antmicro/gpu-cluster-backplane/assets/previews/layer0.png

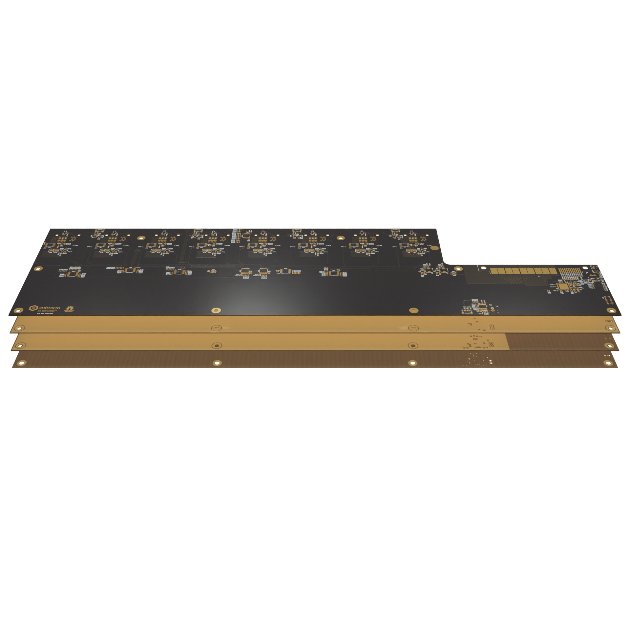
assets/previews/layer0.png
