antmicro/gpu-cluster-backplane/assets/previews/layer2.png

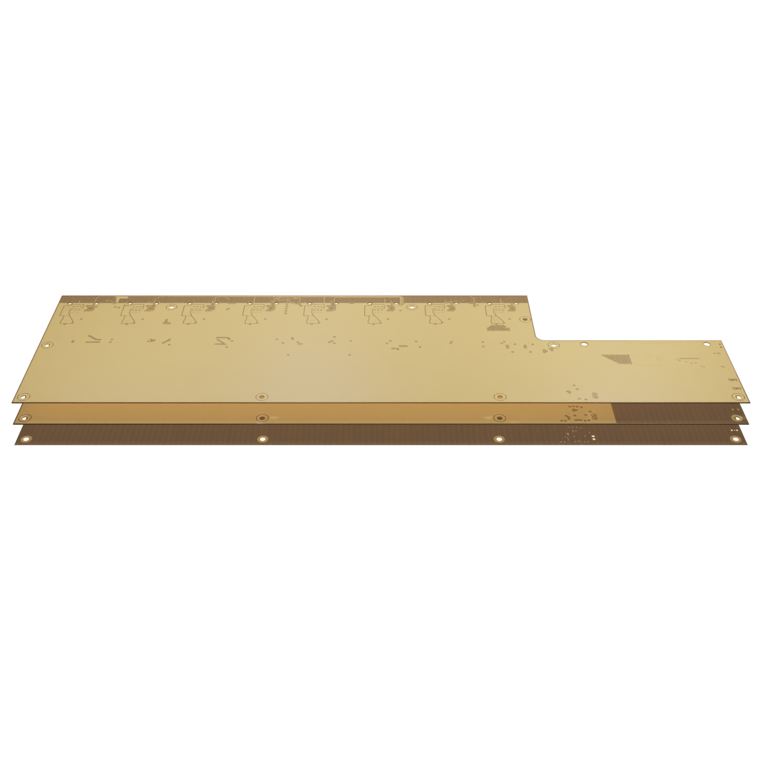
assets/previews/layer2.png
