antmicro/gpu-cluster-backplane/assets/previews/leftB.png

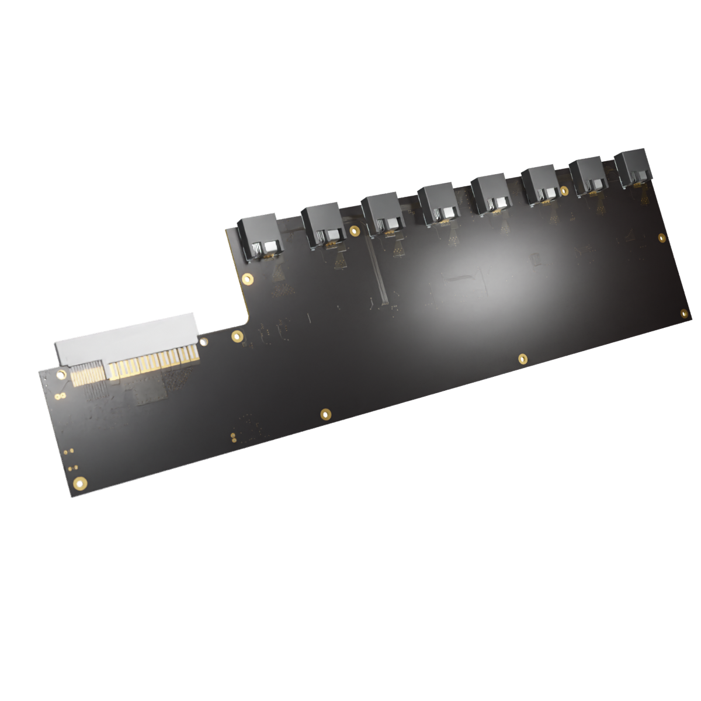
assets/previews/leftB.png
