antmicro/gpu-cluster-backplane/assets/previews/leftT.png

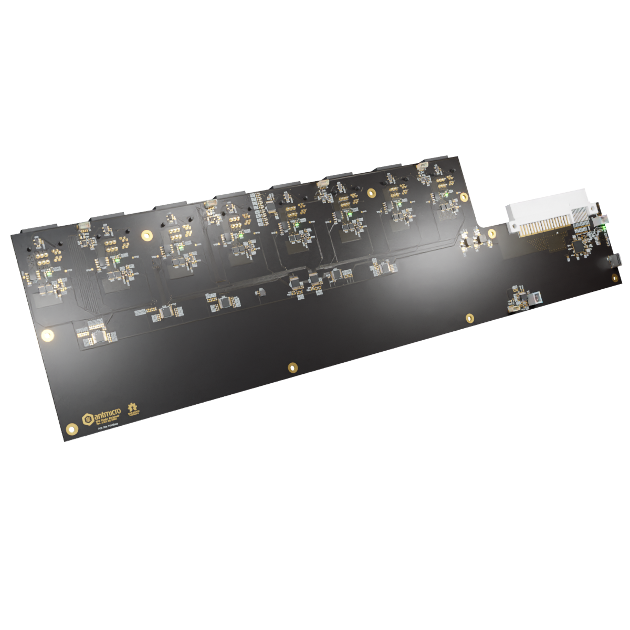
assets/previews/leftT.png
