antmicro/gpu-cluster-backplane/assets/previews/orthoB.png

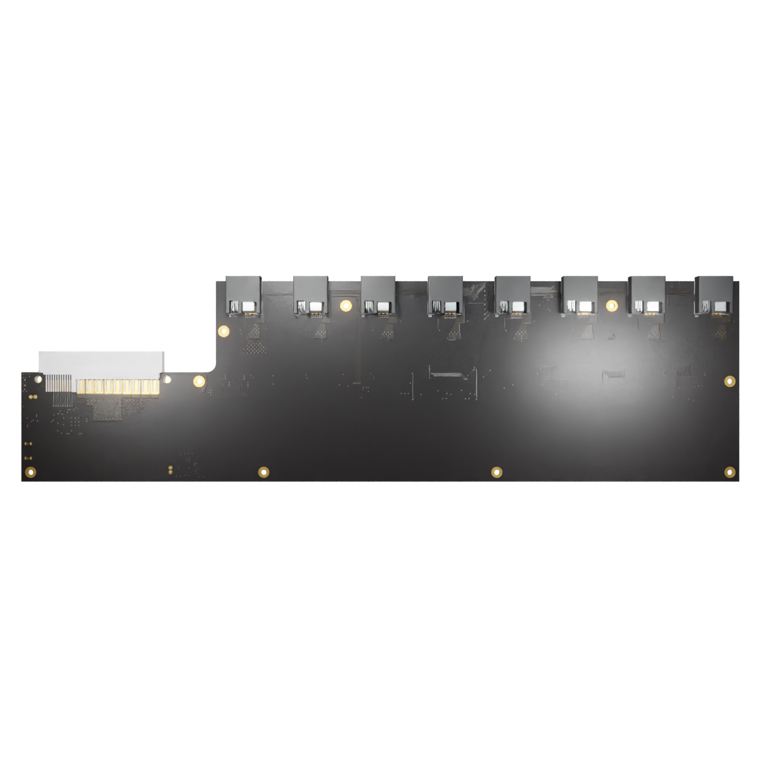
assets/previews/orthoB.png
