antmicro/gpu-cluster-backplane/assets/previews/orthoB_thumbnail.png

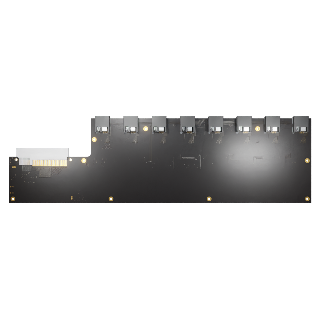
assets/previews/orthoB_thumbnail.png
