antmicro/gpu-cluster-backplane/assets/previews/orthoT.png

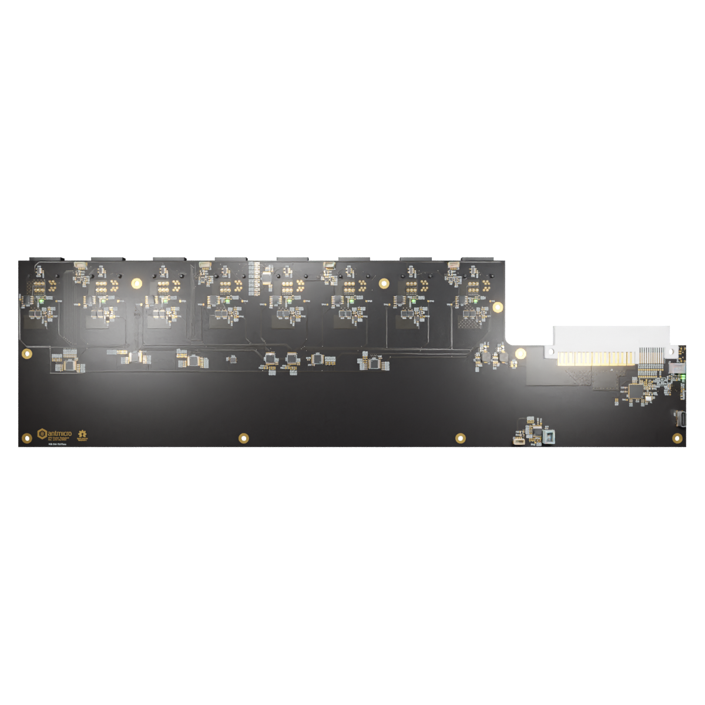
assets/previews/orthoT.png
