antmicro/gpu-cluster-backplane/assets/previews/photoB.png

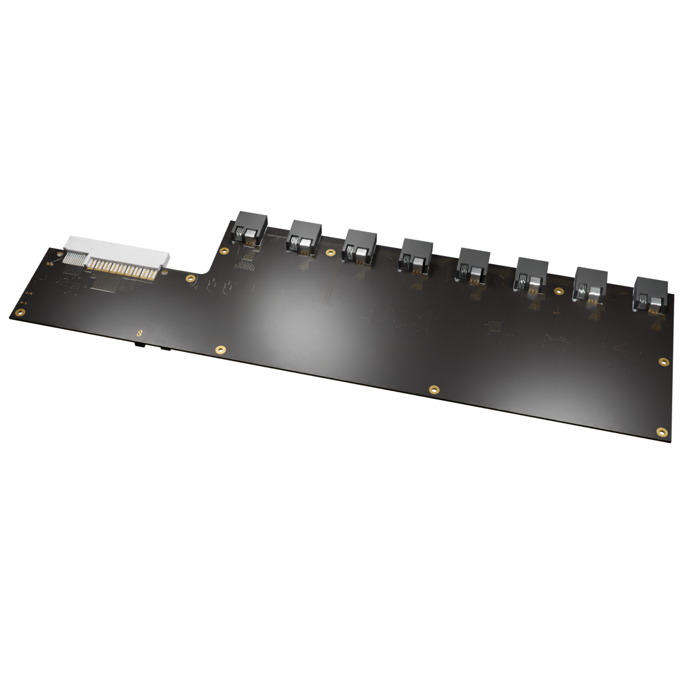
assets/previews/photoB.png
