antmicro/gpu-cluster-backplane/assets/previews/photoT.png

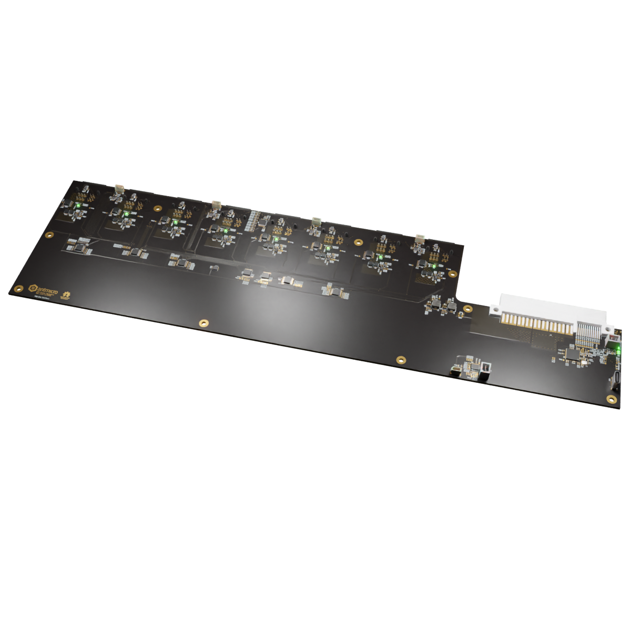
assets/previews/photoT.png
