antmicro/gpu-cluster-backplane/assets/previews/rightB.png

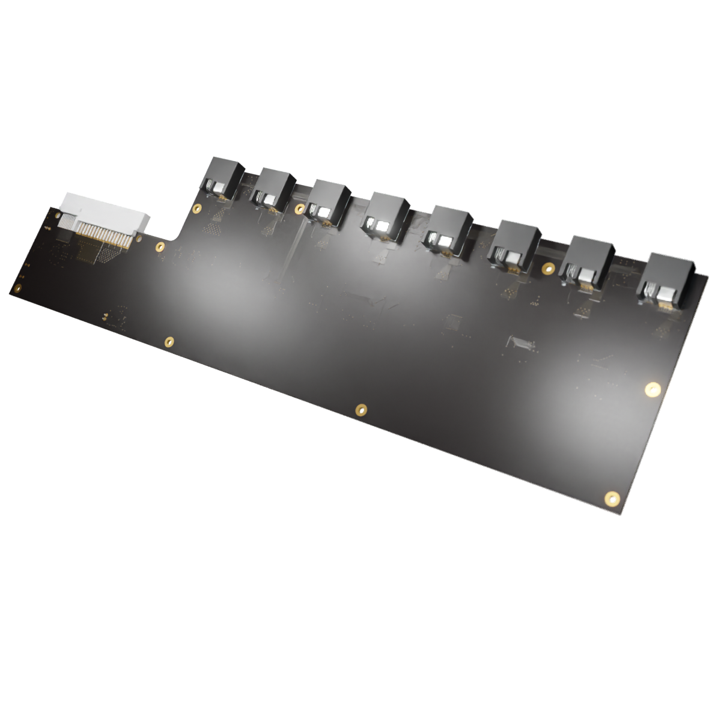
assets/previews/rightB.png
