antmicro/gpu-cluster-backplane/assets/previews/rightT.png

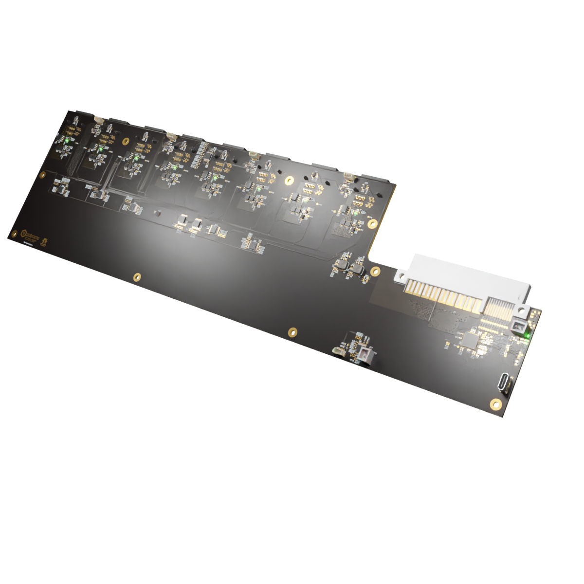
assets/previews/rightT.png
