antmicro/gpu-cluster-backplane/GPU-output.kicad_sch

## KiCad design GPU-output.kicad_sch (2023-11-16)

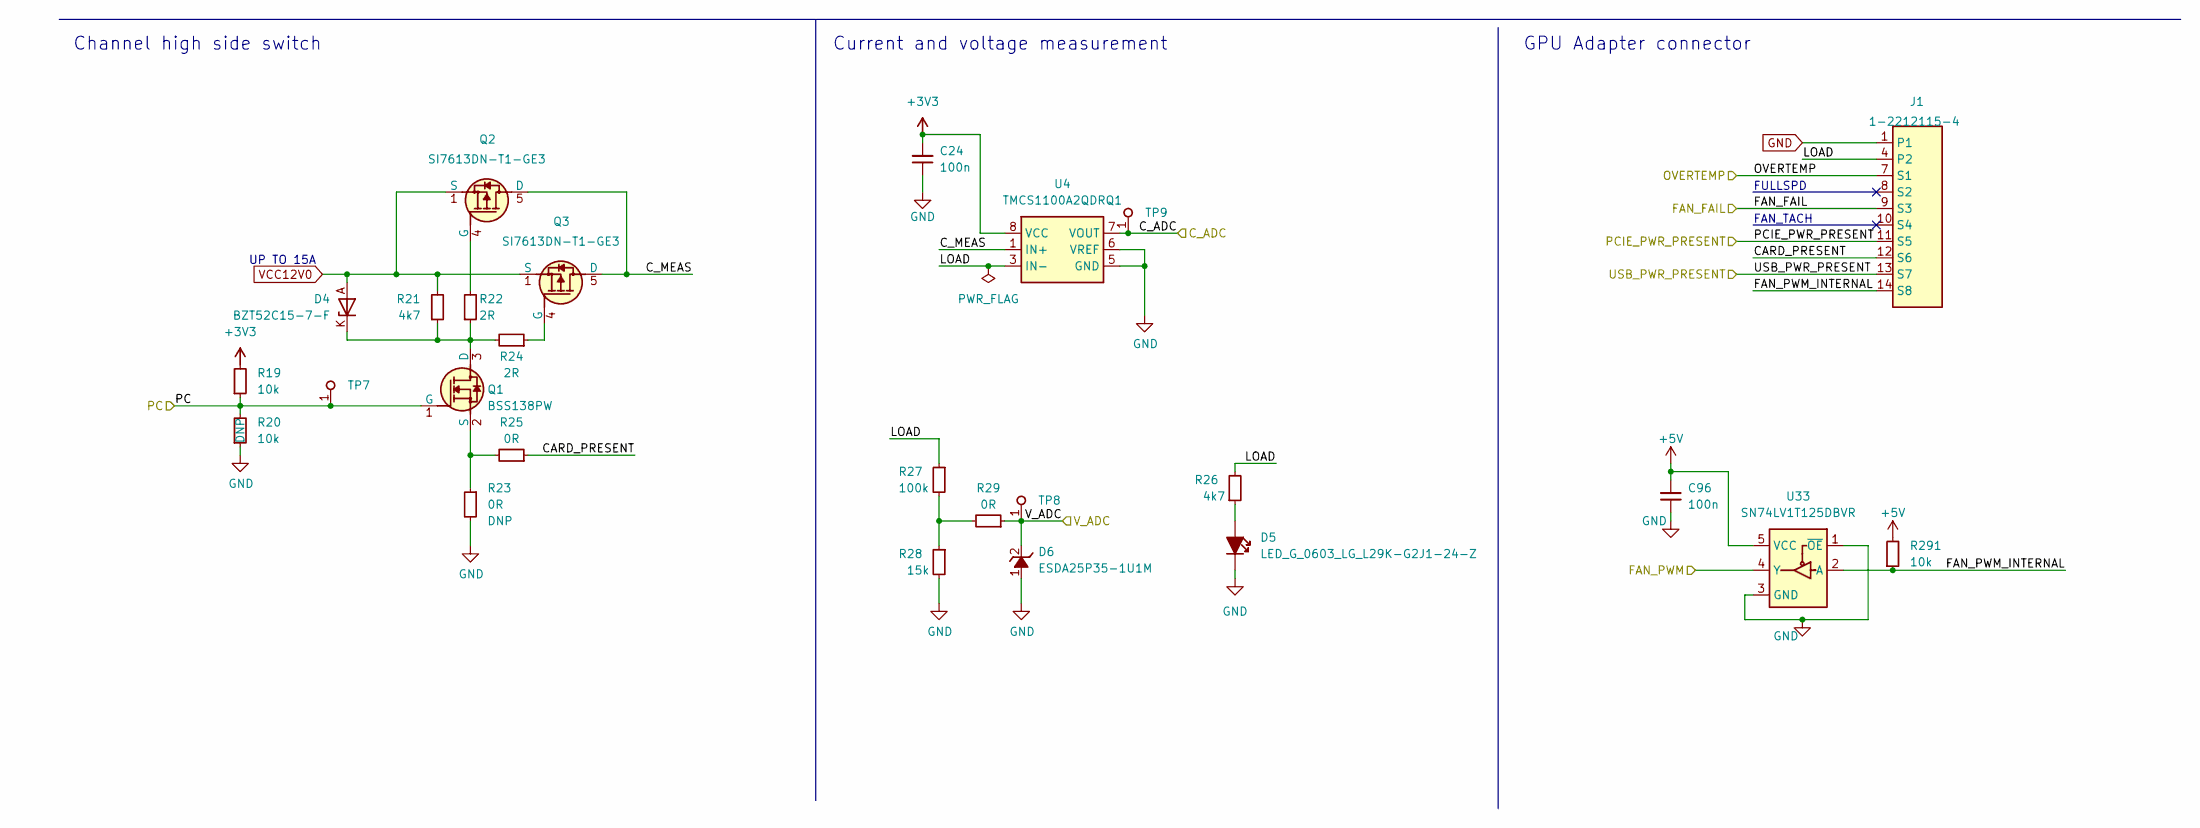
[picture p28: schematic GPU-output.kicad_sch]

Parts:
C24, C96: C_100n_0402; C_0402_1005Metric; Voltage 50V; MPN GRM155R61H104KE14D
D4: BZT52C15-7-F; D_SOD-123F; MPN BZT52C15-7-F
D5: LED_G_0603_LG_L29K-G2J1-24-Z; LED_0603_1608Metric_G; MPN LG L29K-G2J1-24-Z
D6: ESDA25P35-1U1M; MPN ESDA25P35-1U1M
J1: Conn_1-2212115-4; MPN 1-2212115-4
Q1: BSS138PW; SC70-3; MPN BSS138PW
Q2, Q3: SI7613DN-T1-GE3; Vishay_PowerPAK_1212-8_Single; MPN SI7613DN-T1-GE3
R19, R20, R291: R_10k_0402; R_0402_1005Metric; Tolerance 1%; MPN CR0402-FX-1002GLF
R21, R26: R_4k7_0402; R_0402_1005Metric; Tolerance 1%; MPN CR0402-FX-4701GLF
R22, R24: R_2R_0402; R_0402_1005Metric; Tolerance 1%; MPN CR0402-FX-2R00GLF
R23, R25, R29: R_0R_0402; R_0402_1005Metric; MPN ERJ2GE0R00X
R27: R_100k_0402; R_0402_1005Metric; Tolerance 1%; MPN CR0402-FX-1003GLF
R28: R_15k_0.1%_0402; R_0402_1005Metric; Tolerance 0.1%; MPN ERA-2ARB153X
TP7, TP8, TP9: TP_1mm_SMD; TP_SMD_1mm
U4: TMCS1100A2-Q1; SOIC-8_3.9x4.9x1.75mm_P1.27mm; MPN TMCS1100A2QDRQ1
U33: SN74LV1T125DBVR; SOT-23-5; MPN SN74LV1T125DBVR

Connections:
+3V3: C24.2, R19.2, U4.8 (VCC)
+5V: C96.2, R291.2, U33.5 (VCC)
CARD_PRESENT: J1.12 (S6), R25.1
C_ADC: TP9.1, U4.7 (VOUT)
C_MEAS: Q2.5 (D), Q3.5 (D), U4.1 (IN+), U4.2 (IN+)
FAN_FAIL: J1.9 (S3)
FAN_PWM: U33.4 (Y)
FAN_PWM_INTERNAL: J1.14 (S8), R291.1, U33.2 (A)
GND: C24.1, C96.1, D5.2, D6.1 (K), J1.1, R20.1, R23.2, R28.2, U4.5 (GND), U4.6 (VREF), U33.1 (~OE), U33.3 (GND)
LOAD: J1.4 (P2), R26.2, R27.1, U4.3 (IN-), U4.4 (IN-)
unnamed: D4.K, Q1.3 (D), R21.1, R22.1, R24.2
unnamed: D5.1, R26.1
unnamed: Q1.2 (S), R23.1, R25.2
unnamed: Q2.4 (G), R22.2
unnamed: Q3.4 (G), R24.1
unnamed: R27.2, R28.1, R29.2
OVERTEMP: J1.7 (S1)
PC: Q1.1 (G), R19.1, R20.2, TP7.1
PCIE_PWR_PRESENT: J1.11 (S5)
USB_PWR_PRESENT: J1.13 (S7)
VCC12V0: D4.A, Q2.1 (S), Q2.2 (S), Q2.3 (S), Q3.1 (S), Q3.2 (S), Q3.3 (S), R21.2
V_ADC: D6.2 (A), R29.1, TP8.1

Notes on the sheet:
UP TO 15A
FAN_TACH
Channel high side switch
GPU Adapter connector
Current and voltage measurement
FULLSPD
