antmicro/gpu-cluster-backplane/connectors.kicad_sch

## KiCad design connectors.kicad_sch (2023-11-16)

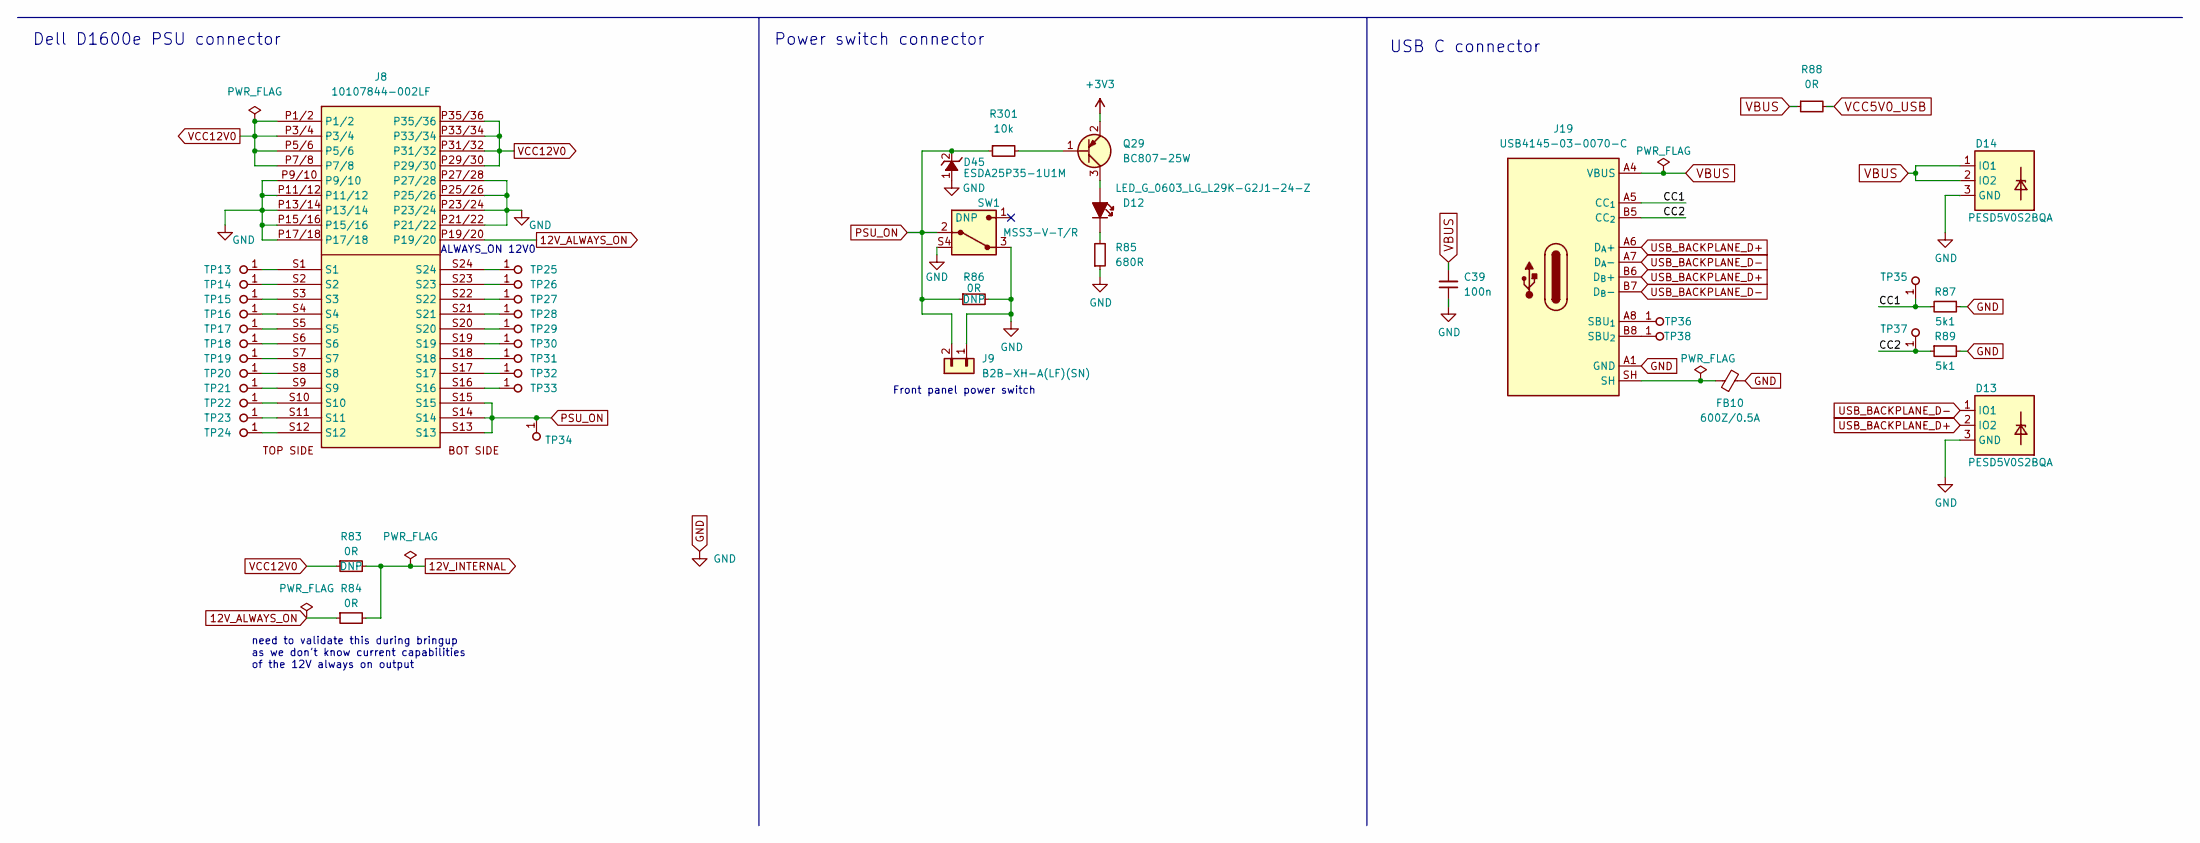
[picture p29: schematic connectors.kicad_sch]

Parts:
C39: C_100n_0402; C_0402_1005Metric; Voltage 50V; MPN GRM155R61H104KE14D
D12: LED_G_0603_LG_L29K-G2J1-24-Z; LED_0603_1608Metric_G; MPN LG L29K-G2J1-24-Z
D13, D14: PESD5V0S2BQA; TPD2E009DRTR; MPN PESD5V0S2BQA
D45: ESDA25P35-1U1M; MPN ESDA25P35-1U1M
FB10: FB_600Z_0.5A_Murata-BLM18AG_0603; FB_0603_1608Metric; MPN BLM18AG601SN1D
J8: Socket_10107844-002LF; MPN 10107844-002LF
J9: JST_XH_1x2_B2B-XH-A-LF-SN; Conn_JST_XH_1x2_B2B-XH-A-LF-SN; MPN B2B-XH-A(LF)(SN)
J19: USB-C_GCT_USB4145-03-0070-C; USB-C_Receptacle_GCT_USB4145-03-0070-C; MPN USB4145-03-0070-C
Q29: BC807-25W; SOT-323; MPN SBC807-40WT1G
R83, R84: R_0R_0805; R_0805_2012Metric; MPN CRCW08050000Z0EA
R85: R_680R_0402; R_0402_1005Metric; Tolerance 1%; MPN CR0402-FX-6800GLF
R86, R88: R_0R_0402; R_0402_1005Metric; MPN ERJ2GE0R00X
R87, R89: R_5k1_0402; R_0402_1005Metric; Tolerance 1%; MPN CR0402-FX-5101GLF
R301: R_10k_0402; R_0402_1005Metric; Tolerance 1%; MPN CR0402-FX-1002GLF
SW1: MSS3-V-T_R; Switch_Slide_MSS3; MPN MSS3-V-T/R
TP13, TP14, TP15, TP16, TP17, TP18, TP19, TP20, TP21, TP22, TP23, TP24, TP25, TP26, TP27, TP28, TP29, TP30, TP31, TP32, TP33, TP34, TP35, TP36, TP37, TP38: TP_1mm_SMD; TP_SMD_1mm

Connections:
12V_ALWAYS_ON: J8.P19/20, R84.1
12V_INTERNAL: R83.2, R84.2
+3V3: Q29.2
CC1: J19.A5 (CC_{1}), R87.2, TP35.1
CC2: J19.B5 (CC_{2}), R89.1, TP37.1
GND: C39.1, D13.3 (GND), D14.3 (GND), D45.1 (K), FB10.2, J8.P9/10, J8.P11/12, J8.P13/14, J8.P15/16, J8.P17/18, J8.P21/22, J8.P23/24, J8.P25/26, J8.P27/28, J9.1, J19.A1 (GND), J19.A12 (GND), J19.B1 (GND), J19.B12 (GND), R85.1, R86.2, R87.1, R89.2, SW1.3, SW1.S1 (SH), SW1.S2 (SH), SW1.S3 (SH), SW1.S4 (SH)
unnamed: D12.1, Q29.3
unnamed: D12.2, R85.2
unnamed: FB10.1, J19.SH
unnamed: J8.S1, TP13.1
unnamed: J8.S2, TP14.1
unnamed: J8.S3, TP15.1
unnamed: J8.S4, TP16.1
unnamed: J8.S5, TP17.1
unnamed: J8.S6, TP18.1
unnamed: J8.S7, TP19.1
unnamed: J8.S8, TP20.1
unnamed: J8.S9, TP21.1
unnamed: J8.S10, TP22.1
unnamed: J8.S11, TP23.1
unnamed: J8.S12, TP24.1
unnamed: J8.S16, TP33.1
unnamed: J8.S17, TP32.1
unnamed: J8.S18, TP31.1
unnamed: J8.S19, TP30.1
unnamed: J8.S20, TP29.1
unnamed: J8.S21, TP28.1
unnamed: J8.S22, TP27.1
unnamed: J8.S23, TP26.1
unnamed: J8.S24, TP25.1
unnamed: J19.A8 (SBU_{1}), TP36.1
unnamed: J19.B8 (SBU_{2}), TP38.1
unnamed: Q29.1, R301.2
PSU_ON: D45.2 (A), J8.S13, J8.S14, J8.S15, J9.2, R86.1, R301.1, SW1.2, TP34.1
USB_BACKPLANE_D+: D13.2 (IO2), J19.A6 (D_{A}+), J19.B6 (D_{B}+)
USB_BACKPLANE_D-: D13.1 (IO1), J19.A7 (D_{A}-), J19.B7 (D_{B}-)
VBUS: C39.2, D14.1 (IO1), D14.2 (IO2), J19.A4 (VBUS), J19.A9 (VBUS), J19.B4 (VBUS), J19.B9 (VBUS), R88.1
VCC5V0_USB: R88.2
VCC12V0: J8.P1/2, J8.P3/4, J8.P5/6, J8.P7/8, J8.P29/30, J8.P31/32, J8.P33/34, J8.P35/36, R83.1

Notes on the sheet:
Dell D1600e PSU connector
Power switch connector
need to validate this during bringup as we don't know current capabilities of the 12V always on output
USB C connector
Front panel power switch
ALWAYS_ON 12V0
