antmicro/gpu-cluster-backplane/debug-signals.kicad_sch

## KiCad design debug-signals.kicad_sch (2023-11-15)

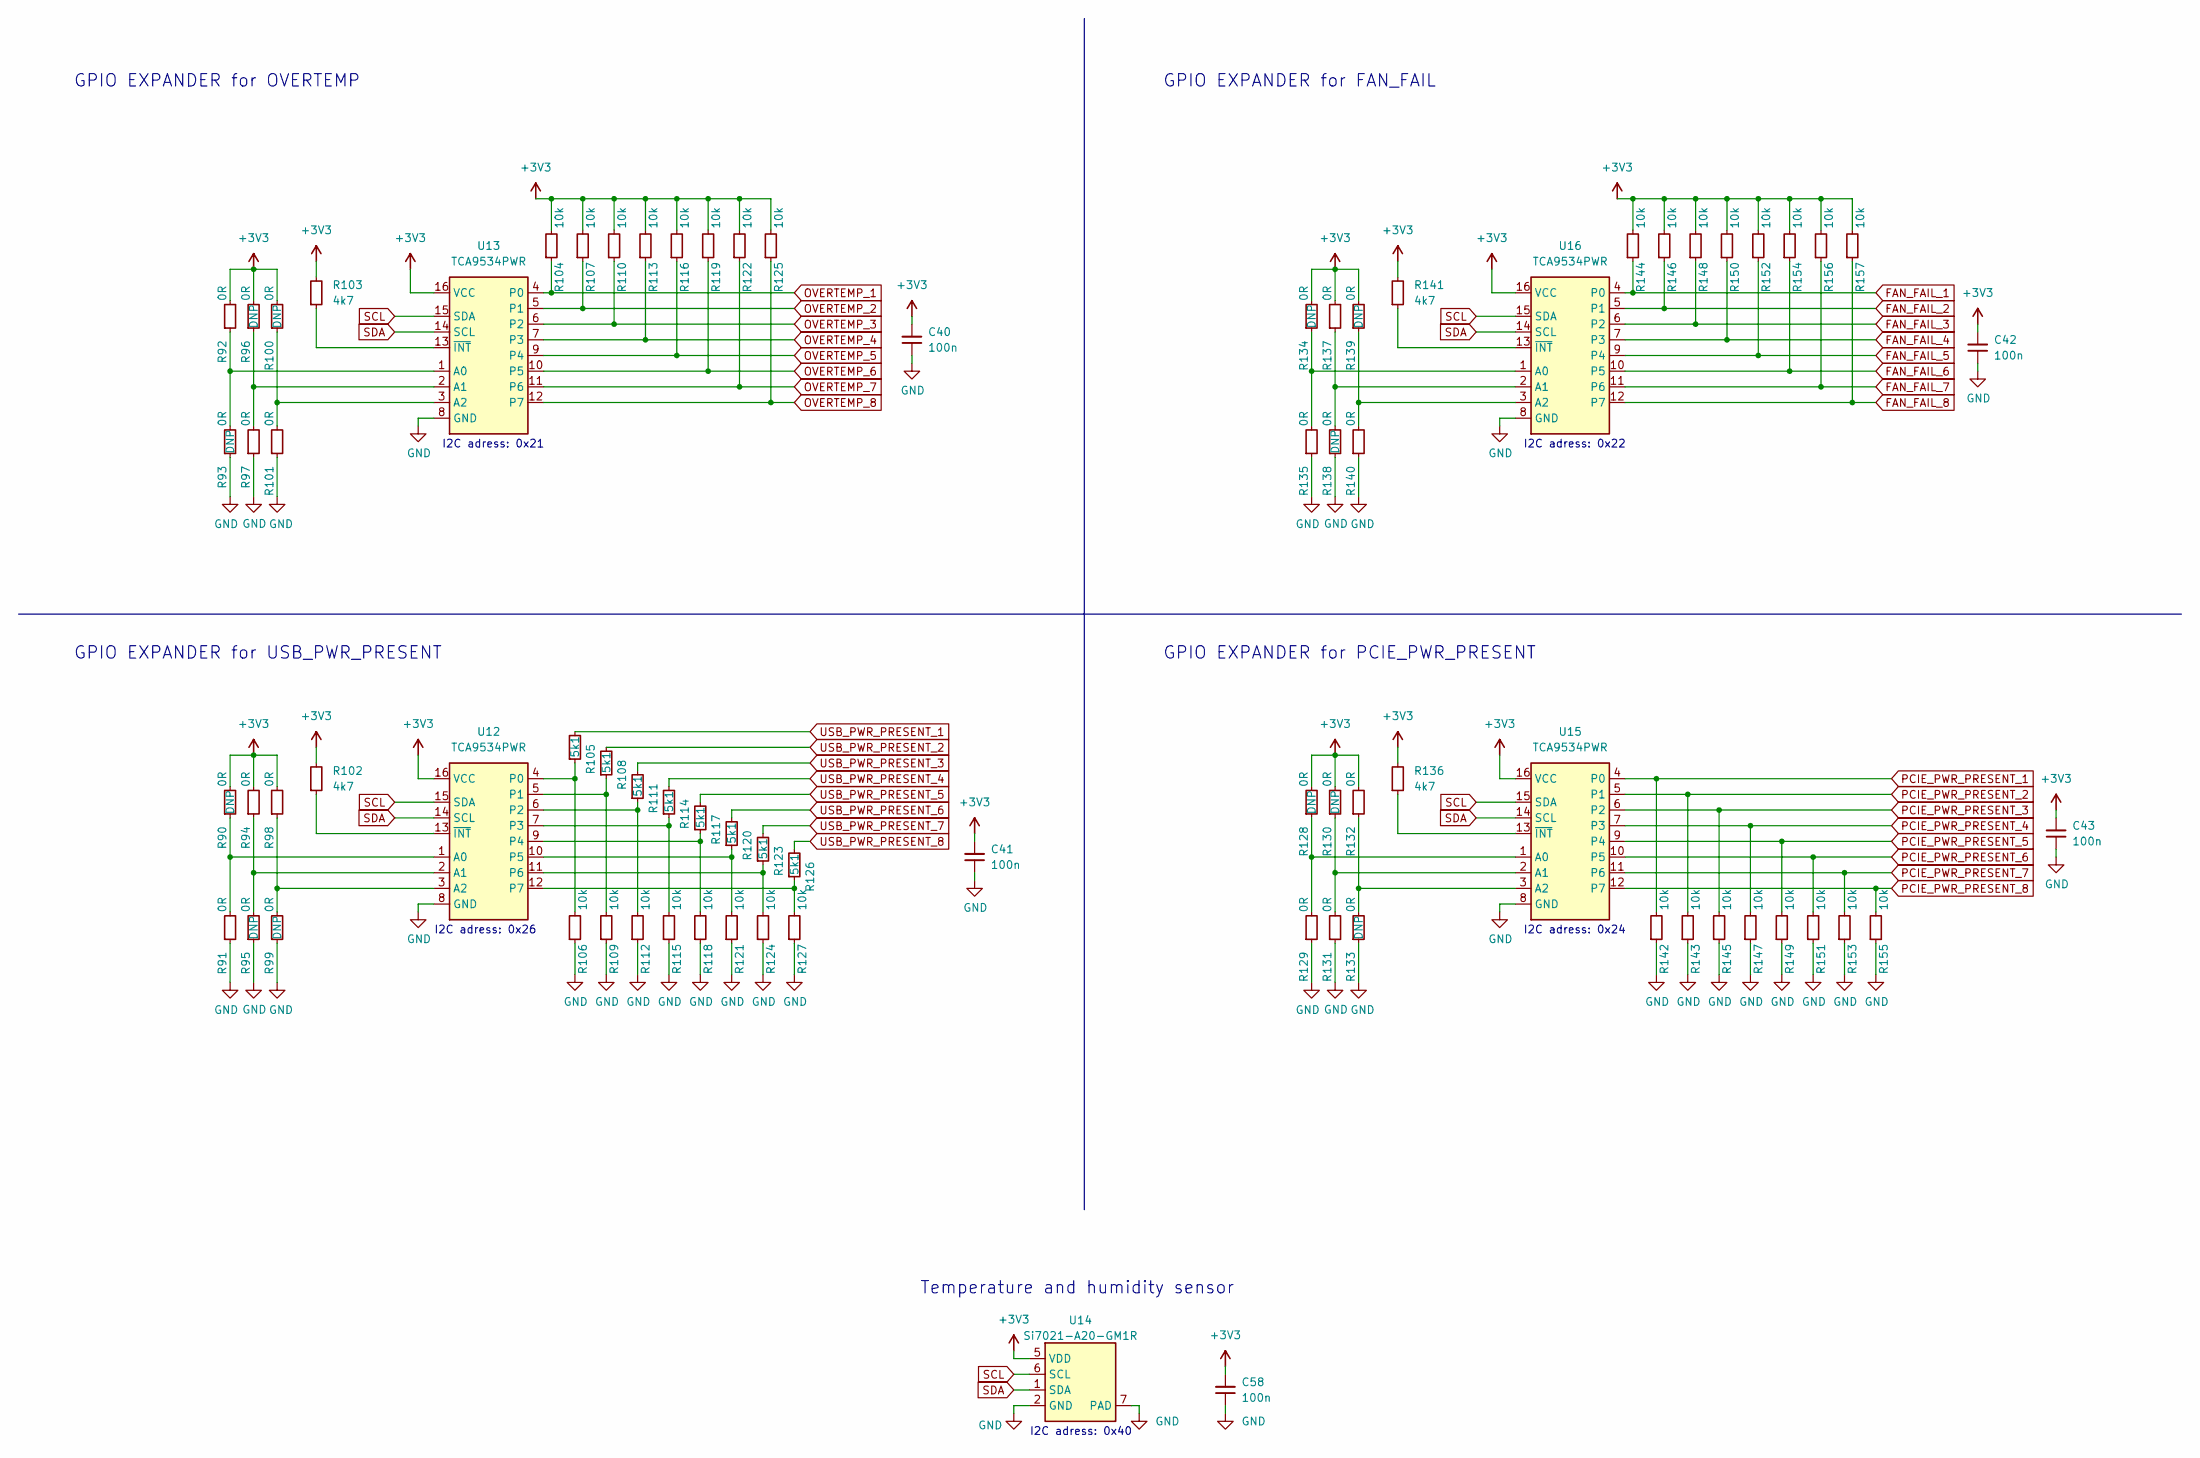
[picture p30: schematic debug-signals.kicad_sch]

Parts:
C40, C41, C42, C43, C58: C_100n_0402; C_0402_1005Metric; Voltage 50V; MPN GRM155R61H104KE14D
R90, R91, R92, R93, R94, R95, R96, R97, R98, R99, R100, R101, R128, R129, R130, R131, R132, R133, R134, R135, R137, R138, R139, R140: R_0R_0402; R_0402_1005Metric; MPN ERJ2GE0R00X
R102, R103, R136, R141: R_4k7_0402; R_0402_1005Metric; Tolerance 1%; MPN CR0402-FX-4701GLF
R104, R106, R107, R109, R110, R112, R113, R115, R116, R118, R119, R121, R122, R124, R125, R127, R142, R143, R144, R145, R146, R147, R148, R149, R150, R151, R152, R153, R154, R155, R156, R157: R_10k_0402; R_0402_1005Metric; Tolerance 1%; MPN CR0402-FX-1002GLF
R105, R108, R111, R114, R117, R120, R123, R126: R_5k1_0402; R_0402_1005Metric; Tolerance 1%; MPN CR0402-FX-5101GLF
U12, U13, U15, U16: TCA9534PWR_TSSOP; TSSOP-16_4.4x5mm_P0.65mm; MPN TCA9534PWR
U14: Si7021; DFN-6-1EP_3x3mm_P1mm_EP1.5x2.4mm; MPN Si7021-A20-GM1R

Connections:
+3V3: C40.2, C41.2, C42.2, C43.2, C58.2, R90.2, R92.2, R94.2, R96.2, R98.2, R100.2, R102.2, R103.2, R104.2, R107.2, R110.2, R113.2, R116.2, R119.2, R122.2, R125.2, R128.2, R130.2, R132.2, R134.2, R136.2, R137.2, R139.2, R141.2, R144.2, R146.2, R148.2, R150.2, R152.2, R154.2, R156.2, R157.2, U12.16 (VCC), U13.16 (VCC), U14.5 (VDD), U15.16 (VCC), U16.16 (VCC)
FAN_FAIL_1: R144.1, U16.4 (P0)
FAN_FAIL_2: R146.1, U16.5 (P1)
FAN_FAIL_3: R148.1, U16.6 (P2)
FAN_FAIL_4: R150.1, U16.7 (P3)
FAN_FAIL_5: R152.1, U16.9 (P4)
FAN_FAIL_6: R154.1, U16.10 (P5)
FAN_FAIL_7: R156.1, U16.11 (P6)
FAN_FAIL_8: R157.1, U16.12 (P7)
GND: C40.1, C41.1, C42.1, C43.1, C58.1, R91.1, R93.1, R95.1, R97.1, R99.1, R101.1, R106.1, R109.1, R112.1, R115.1, R118.1, R121.1, R124.1, R127.1, R129.1, R131.1, R133.1, R135.1, R138.1, R140.1, R142.1, R143.1, R145.1, R147.1, R149.1, R151.1, R153.1, R155.1, U12.8 (GND), U13.8 (GND), U14.2 (GND), U14.7 (PAD), U15.8 (GND), U16.8 (GND)
unnamed: R90.1, R91.2, U12.1 (A0)
unnamed: R92.1, R93.2, U13.1 (A0)
unnamed: R94.1, R95.2, U12.2 (A1)
unnamed: R96.1, R97.2, U13.2 (A1)
unnamed: R98.1, R99.2, U12.3 (A2)
unnamed: R100.1, R101.2, U13.3 (A2)
unnamed: R102.1, U12.13 (~INT)
unnamed: R103.1, U13.13 (~INT)
unnamed: R105.1, R106.2, U12.4 (P0)
unnamed: R108.1, R109.2, U12.5 (P1)
unnamed: R111.1, R112.2, U12.6 (P2)
unnamed: R114.1, R115.2, U12.7 (P3)
unnamed: R117.1, R118.2, U12.9 (P4)
unnamed: R120.1, R121.2, U12.10 (P5)
unnamed: R123.1, R124.2, U12.11 (P6)
unnamed: R126.1, R127.2, U12.12 (P7)
unnamed: R128.1, R129.2, U15.1 (A0)
unnamed: R130.1, R131.2, U15.2 (A1)
unnamed: R132.1, R133.2, U15.3 (A2)
unnamed: R134.1, R135.2, U16.1 (A0)
unnamed: R136.1, U15.13 (~INT)
unnamed: R137.1, R138.2, U16.2 (A1)
unnamed: R139.1, R140.2, U16.3 (A2)
unnamed: R141.1, U16.13 (~INT)
OVERTEMP_1: R104.1, U13.4 (P0)
OVERTEMP_2: R107.1, U13.5 (P1)
OVERTEMP_3: R110.1, U13.6 (P2)
OVERTEMP_4: R113.1, U13.7 (P3)
OVERTEMP_5: R116.1, U13.9 (P4)
OVERTEMP_6: R119.1, U13.10 (P5)
OVERTEMP_7: R122.1, U13.11 (P6)
OVERTEMP_8: R125.1, U13.12 (P7)
PCIE_PWR_PRESENT_1: R142.2, U15.4 (P0)
PCIE_PWR_PRESENT_2: R143.2, U15.5 (P1)
PCIE_PWR_PRESENT_3: R145.2, U15.6 (P2)
PCIE_PWR_PRESENT_4: R147.2, U15.7 (P3)
PCIE_PWR_PRESENT_5: R149.2, U15.9 (P4)
PCIE_PWR_PRESENT_6: R151.2, U15.10 (P5)
PCIE_PWR_PRESENT_7: R153.2, U15.11 (P6)
PCIE_PWR_PRESENT_8: R155.2, U15.12 (P7)
SCL: U12.15 (SDA), U13.15 (SDA), U14.6 (SCL), U15.15 (SDA), U16.15 (SDA)
SDA: U12.14 (SCL), U13.14 (SCL), U14.1 (SDA), U15.14 (SCL), U16.14 (SCL)
USB_PWR_PRESENT_1: R105.2
USB_PWR_PRESENT_2: R108.2
USB_PWR_PRESENT_3: R111.2
USB_PWR_PRESENT_4: R114.2
USB_PWR_PRESENT_5: R117.2
USB_PWR_PRESENT_6: R120.2
USB_PWR_PRESENT_7: R123.2
USB_PWR_PRESENT_8: R126.2

Notes on the sheet:
GPIO EXPANDER for PCIE_PWR_PRESENT
GPIO EXPANDER for FAN_FAIL
I2C adress: 0x21
I2C adress: 0x26
I2C adress: 0x22
I2C adress: 0x24
Temperature and humidity sensor
GPIO EXPANDER for USB_PWR_PRESENT
I2C adress: 0x40
GPIO EXPANDER for OVERTEMP
