antmicro/gpu-cluster-backplane/fans-control.kicad_sch

## KiCad design fans-control.kicad_sch (2023-11-16)

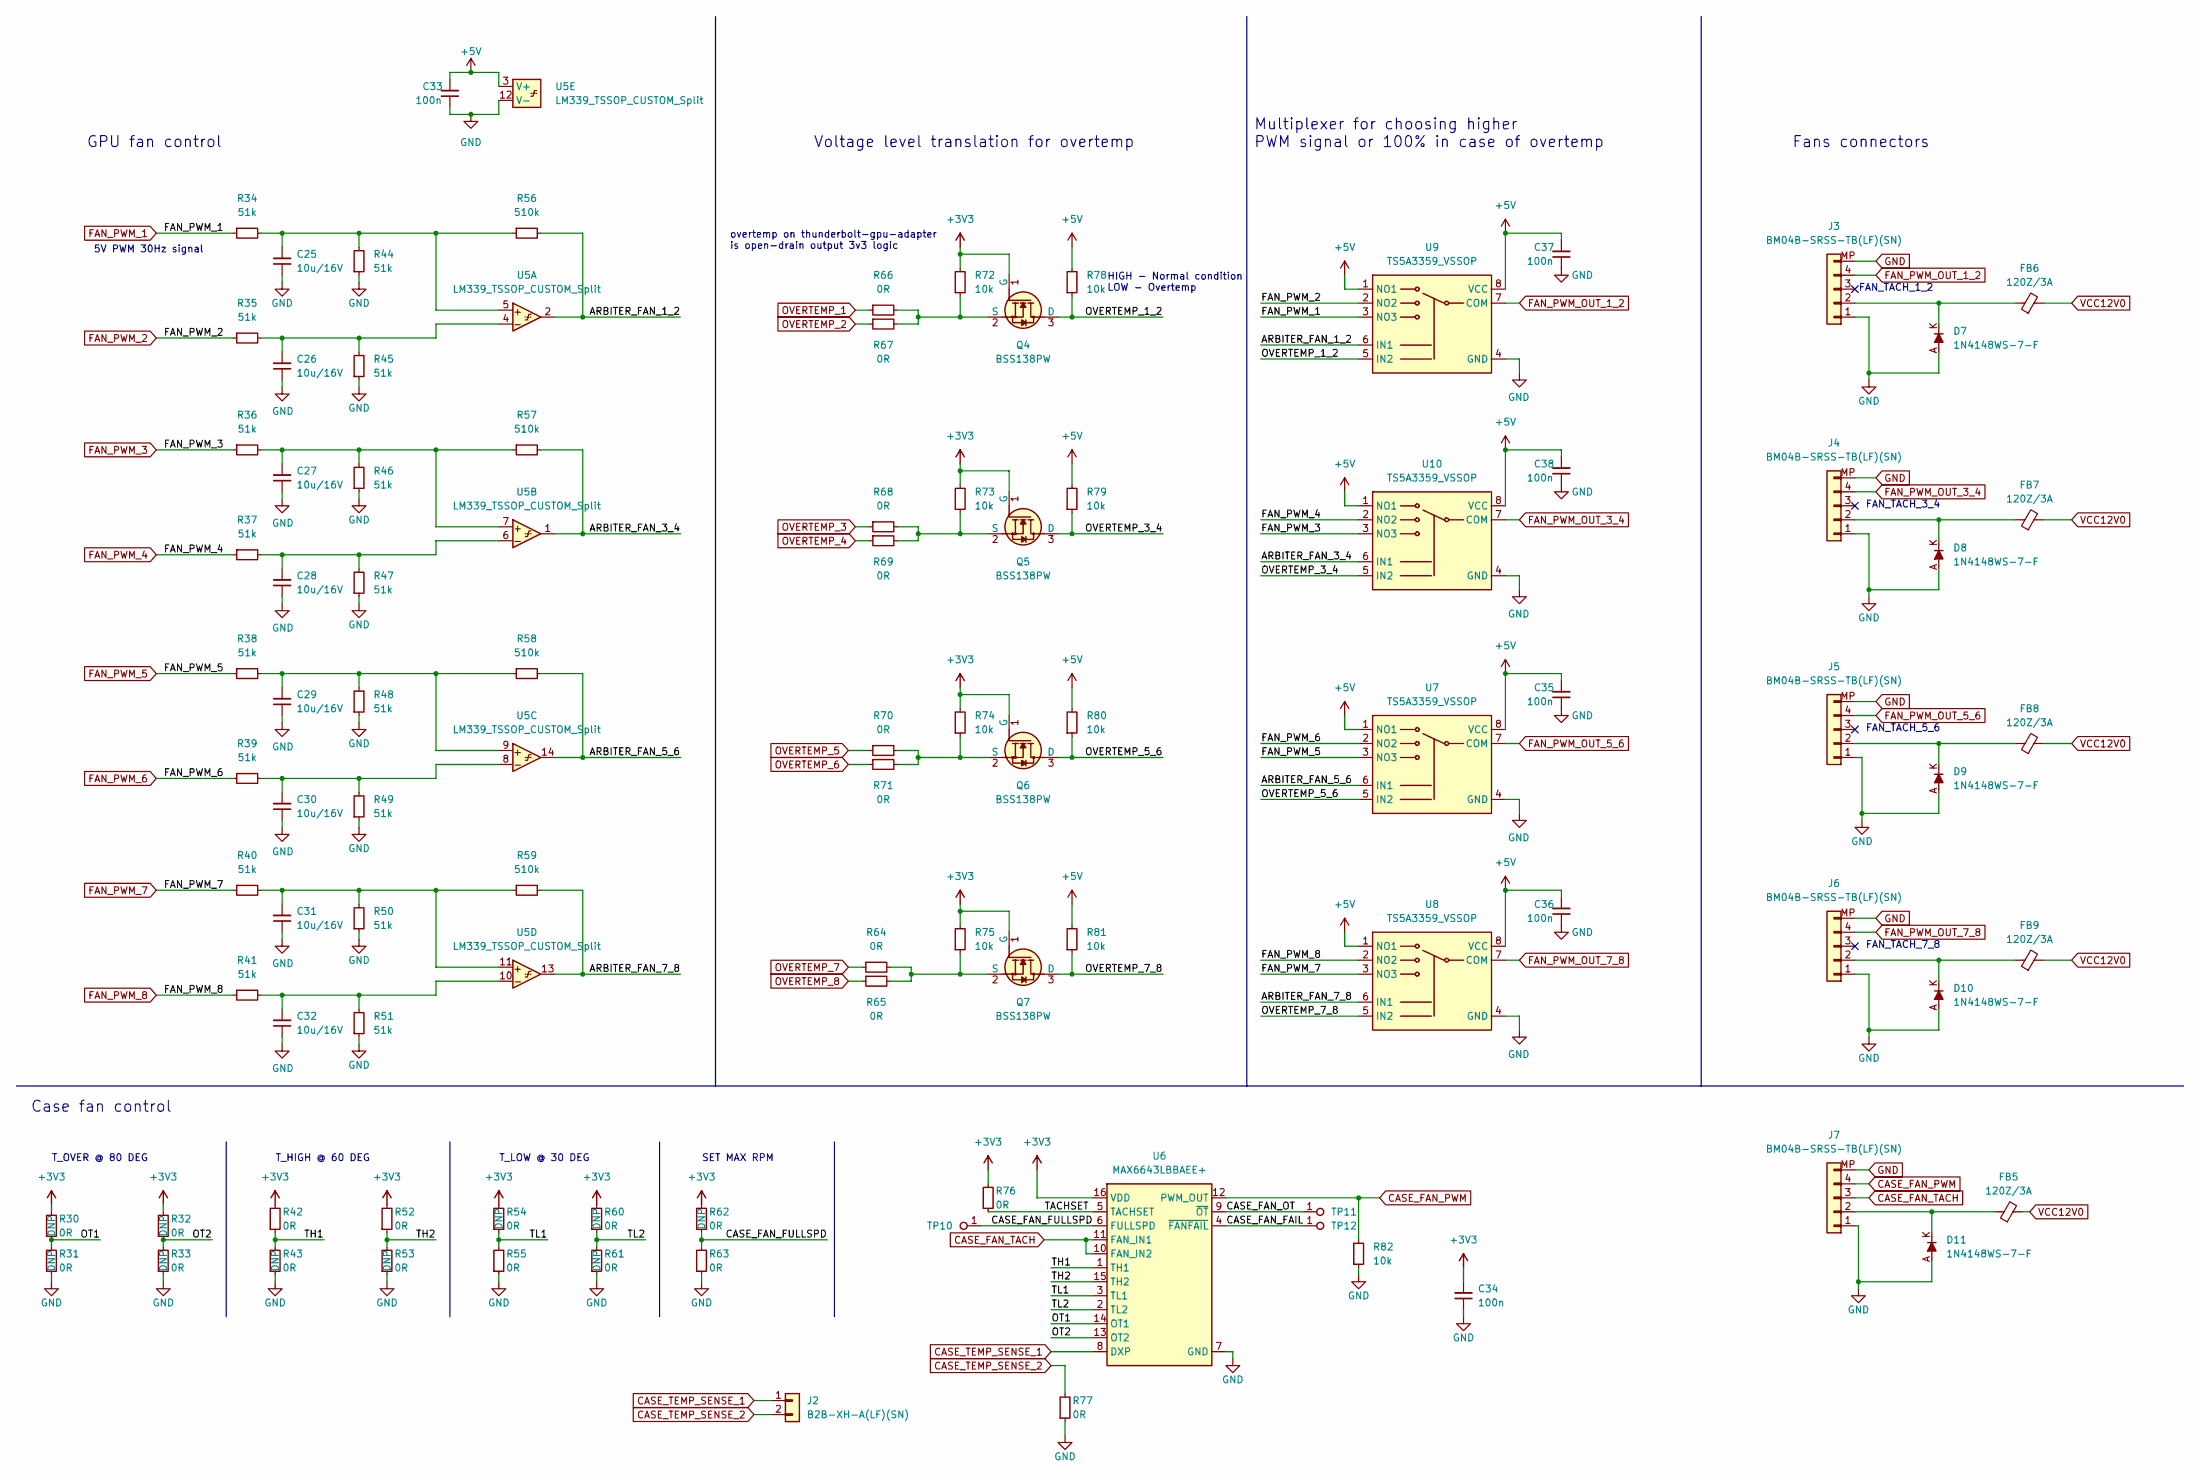
[picture p31: schematic fans-control.kicad_sch]

Parts:
C25, C26, C27, C28, C29, C30, C31, C32: C_10u_16V_0603; C_0603_1608Metric; MPN GRM188C81C106MA73D
C33, C34, C35, C36, C37, C38: C_100n_0402; C_0402_1005Metric; Voltage 50V; MPN GRM155R61H104KE14D
D7, D8, D9, D10, D11: 1N4148WS-7-F; SOD-323; MPN 1N4148WS-7-F
FB5, FB6, FB7, FB8, FB9: FB_120Z_3A_Murata-BLM18SG_0603; FB_0603_1608Metric; MPN BLM18SG121TN1D
J2: JST_XH_1x2_B2B-XH-A-LF-SN; Conn_JST_XH_1x2_B2B-XH-A-LF-SN; MPN B2B-XH-A(LF)(SN)
J3, J4, J5, J6, J7: JST_SH_1x4_BM04B-SRSS-TB-LF-SN; Conn_JST_SH_1x4_BM04B-SRSS-TB-LF-SN; MPN BM04B-SRSS-TB(LF)(SN)
Q4, Q5, Q6, Q7: BSS138PW; SC70-3; MPN BSS138PW
R30, R31, R32, R33, R42, R43, R52, R53, R54, R55, R60, R61, R62, R63, R64, R65, R66, R67, R68, R69, R70, R71, R76, R77: R_0R_0402; R_0402_1005Metric; MPN ERJ2GE0R00X
R34, R35, R36, R37, R38, R39, R40, R41, R44, R45, R46, R47, R48, R49, R50, R51: R_51k_0402; R_0402_1005Metric; Tolerance 1%; MPN CR0402-FX-5102GLF
R56, R57, R58, R59: R_510k_0402; R_0402_1005Metric; Tolerance 1%; MPN CR0402-FX-5103GLF
R72, R73, R74, R75, R78, R79, R80, R81, R82: R_10k_0402; R_0402_1005Metric; Tolerance 1%; MPN CR0402-FX-1002GLF
TP10, TP11, TP12: TP_1mm_SMD; TP_SMD_1mm
U5: LM339_TSSOP_CUSTOM_Split; TSSOP-14_4.4x5mm_P0.65mm; MPN LM339PW
U6: MAX6643_QSOP; QSOP-16_3x4.75x0.75mm_P0.5mm; MPN MAX6643LBBAEE+
U7, U8, U9, U10: TS5A3359_VSSOP; VSSOP-8_2.3x2mm_P0.5mm; MPN TS5A3359DCUR

Connections:
+3V3: C34.2, Q4.1 (G), Q5.1 (G), Q6.1 (G), Q7.1 (G), R30.2, R32.2, R42.2, R52.2, R54.2, R60.2, R62.2, R72.2, R73.2, R74.2, R75.2, R76.2, U6.16 (VDD)
+5V: C33.2, C35.2, C36.2, C37.2, C38.2, R78.2, R79.2, R80.2, R81.2, U5.3 (V+), U7.1 (NO1), U7.8 (VCC), U8.1 (NO1), U8.8 (VCC), U9.1 (NO1), U9.8 (VCC), U10.1 (NO1), U10.8 (VCC)
ARBITER_FAN_1_2: R56.2, U5.2, U9.6 (IN1)
ARBITER_FAN_3_4: R57.2, U5.1, U10.6 (IN1)
ARBITER_FAN_5_6: R58.2, U5.14, U7.6 (IN1)
ARBITER_FAN_7_8: R59.2, U5.13, U8.6 (IN1)
CASE_FAN_FAIL: TP12.1, U6.4 (~FANFAIL)
CASE_FAN_FULLSPD: R62.1, R63.2, TP10.1, U6.6 (FULLSPD)
CASE_FAN_OT: TP11.1, U6.9 (~OT)
CASE_FAN_PWM: J7.4, R82.2, U6.12 (PWM_OUT)
CASE_FAN_TACH: J7.3, U6.10 (FAN_IN2), U6.11 (FAN_IN1)
CASE_TEMP_SENSE_1: J2.1, U6.8 (DXP)
CASE_TEMP_SENSE_2: J2.2, R77.2
FAN_PWM_1: R34.1, U9.3 (NO3)
FAN_PWM_2: R35.1, U9.2 (NO2)
FAN_PWM_3: R36.1, U10.3 (NO3)
FAN_PWM_4: R37.1, U10.2 (NO2)
FAN_PWM_5: R38.1, U7.3 (NO3)
FAN_PWM_6: R39.1, U7.2 (NO2)
FAN_PWM_7: R40.1, U8.3 (NO3)
FAN_PWM_8: R41.1, U8.2 (NO2)
FAN_PWM_OUT_1_2: J3.4, U9.7 (COM)
FAN_PWM_OUT_3_4: J4.4, U10.7 (COM)
FAN_PWM_OUT_5_6: J5.4, U7.7 (COM)
FAN_PWM_OUT_7_8: J6.4, U8.7 (COM)
GND: C25.1, C26.1, C27.1, C28.1, C29.1, C30.1, C31.1, C32.1, C33.1, C34.1, C35.1, C36.1, C37.1, C38.1, D7.A, D8.A, D9.A, D10.A, D11.A, J3.1, J3.MP, J4.1, J4.MP, J5.1, J5.MP, J6.1, J6.MP, J7.1, J7.MP, R31.1, R33.1, R43.1, R44.1, R45.1, R46.1, R47.1, R48.1, R49.1, R50.1, R51.1, R53.1, R55.1, R61.1, R63.1, R77.1, R82.1, U5.12 (V-), U6.7 (GND), U7.4 (GND), U8.4 (GND), U9.4 (GND), U10.4 (GND)
unnamed: C25.2, R34.2, R44.2, R56.1, U5.5
unnamed: C26.2, R35.2, R45.2, U5.4
unnamed: C27.2, R36.2, R46.2, R57.1, U5.7
unnamed: C28.2, R37.2, R47.2, U5.6
unnamed: C29.2, R38.2, R48.2, R58.1, U5.9
unnamed: C30.2, R39.2, R49.2, U5.8
unnamed: C31.2, R40.2, R50.2, R59.1, U5.11
unnamed: C32.2, R41.2, R51.2, U5.10
unnamed: D7.K, FB6.1, J3.2
unnamed: D8.K, FB7.1, J4.2
unnamed: D9.K, FB8.1, J5.2
unnamed: D10.K, FB9.1, J6.2
unnamed: D11.K, FB5.1, J7.2
unnamed: Q4.2 (S), R66.2, R67.2, R72.1
unnamed: Q5.2 (S), R68.2, R69.2, R73.1
unnamed: Q6.2 (S), R70.2, R71.2, R74.1
unnamed: Q7.2 (S), R64.2, R65.2, R75.1
OT1: R30.1, R31.2, U6.14 (OT1)
OT2: R32.1, R33.2, U6.13 (OT2)
OVERTEMP_1: R66.1
OVERTEMP_1_2: Q4.3 (D), R78.1, U9.5 (IN2)
OVERTEMP_2: R67.1
OVERTEMP_3: R68.1
OVERTEMP_3_4: Q5.3 (D), R79.1, U10.5 (IN2)
OVERTEMP_4: R69.1
OVERTEMP_5: R70.1
OVERTEMP_5_6: Q6.3 (D), R80.1, U7.5 (IN2)
OVERTEMP_6: R71.1
OVERTEMP_7: R64.1
OVERTEMP_7_8: Q7.3 (D), R81.1, U8.5 (IN2)
OVERTEMP_8: R65.1
TACHSET: R76.1, U6.5 (TACHSET)
TH1: R42.1, R43.2, U6.1 (TH1)
TH2: R52.1, R53.2, U6.15 (TH2)
TL1: R54.1, R55.2, U6.3 (TL1)
TL2: R60.1, R61.2, U6.2 (TL2)
VCC12V0: FB5.2, FB6.2, FB7.2, FB8.2, FB9.2

Notes on the sheet:
5V PWM 30Hz signal
FAN_TACH_5_6
Multiplexer for choosing higher PWM signal or 100% in case of overtemp
GPU fan control
SET MAX RPM
FAN_TACH_3_4
HIGH - Normal condition LOW - Overtemp
T_OVER @ 80 DEG
FAN_TACH_7_8
T_LOW @ 30 DEG
Voltage level translation for overtemp
T_HIGH @ 60 DEG
Fans connectors
FAN_TACH_1_2
overtemp on thunderbolt-gpu-adapter is open-drain output 3v3 logic
Case fan control
