antmicro/gpu-cluster-backplane/ftdi-module.kicad_sch

## KiCad design ftdi-module.kicad_sch (2023-11-16)

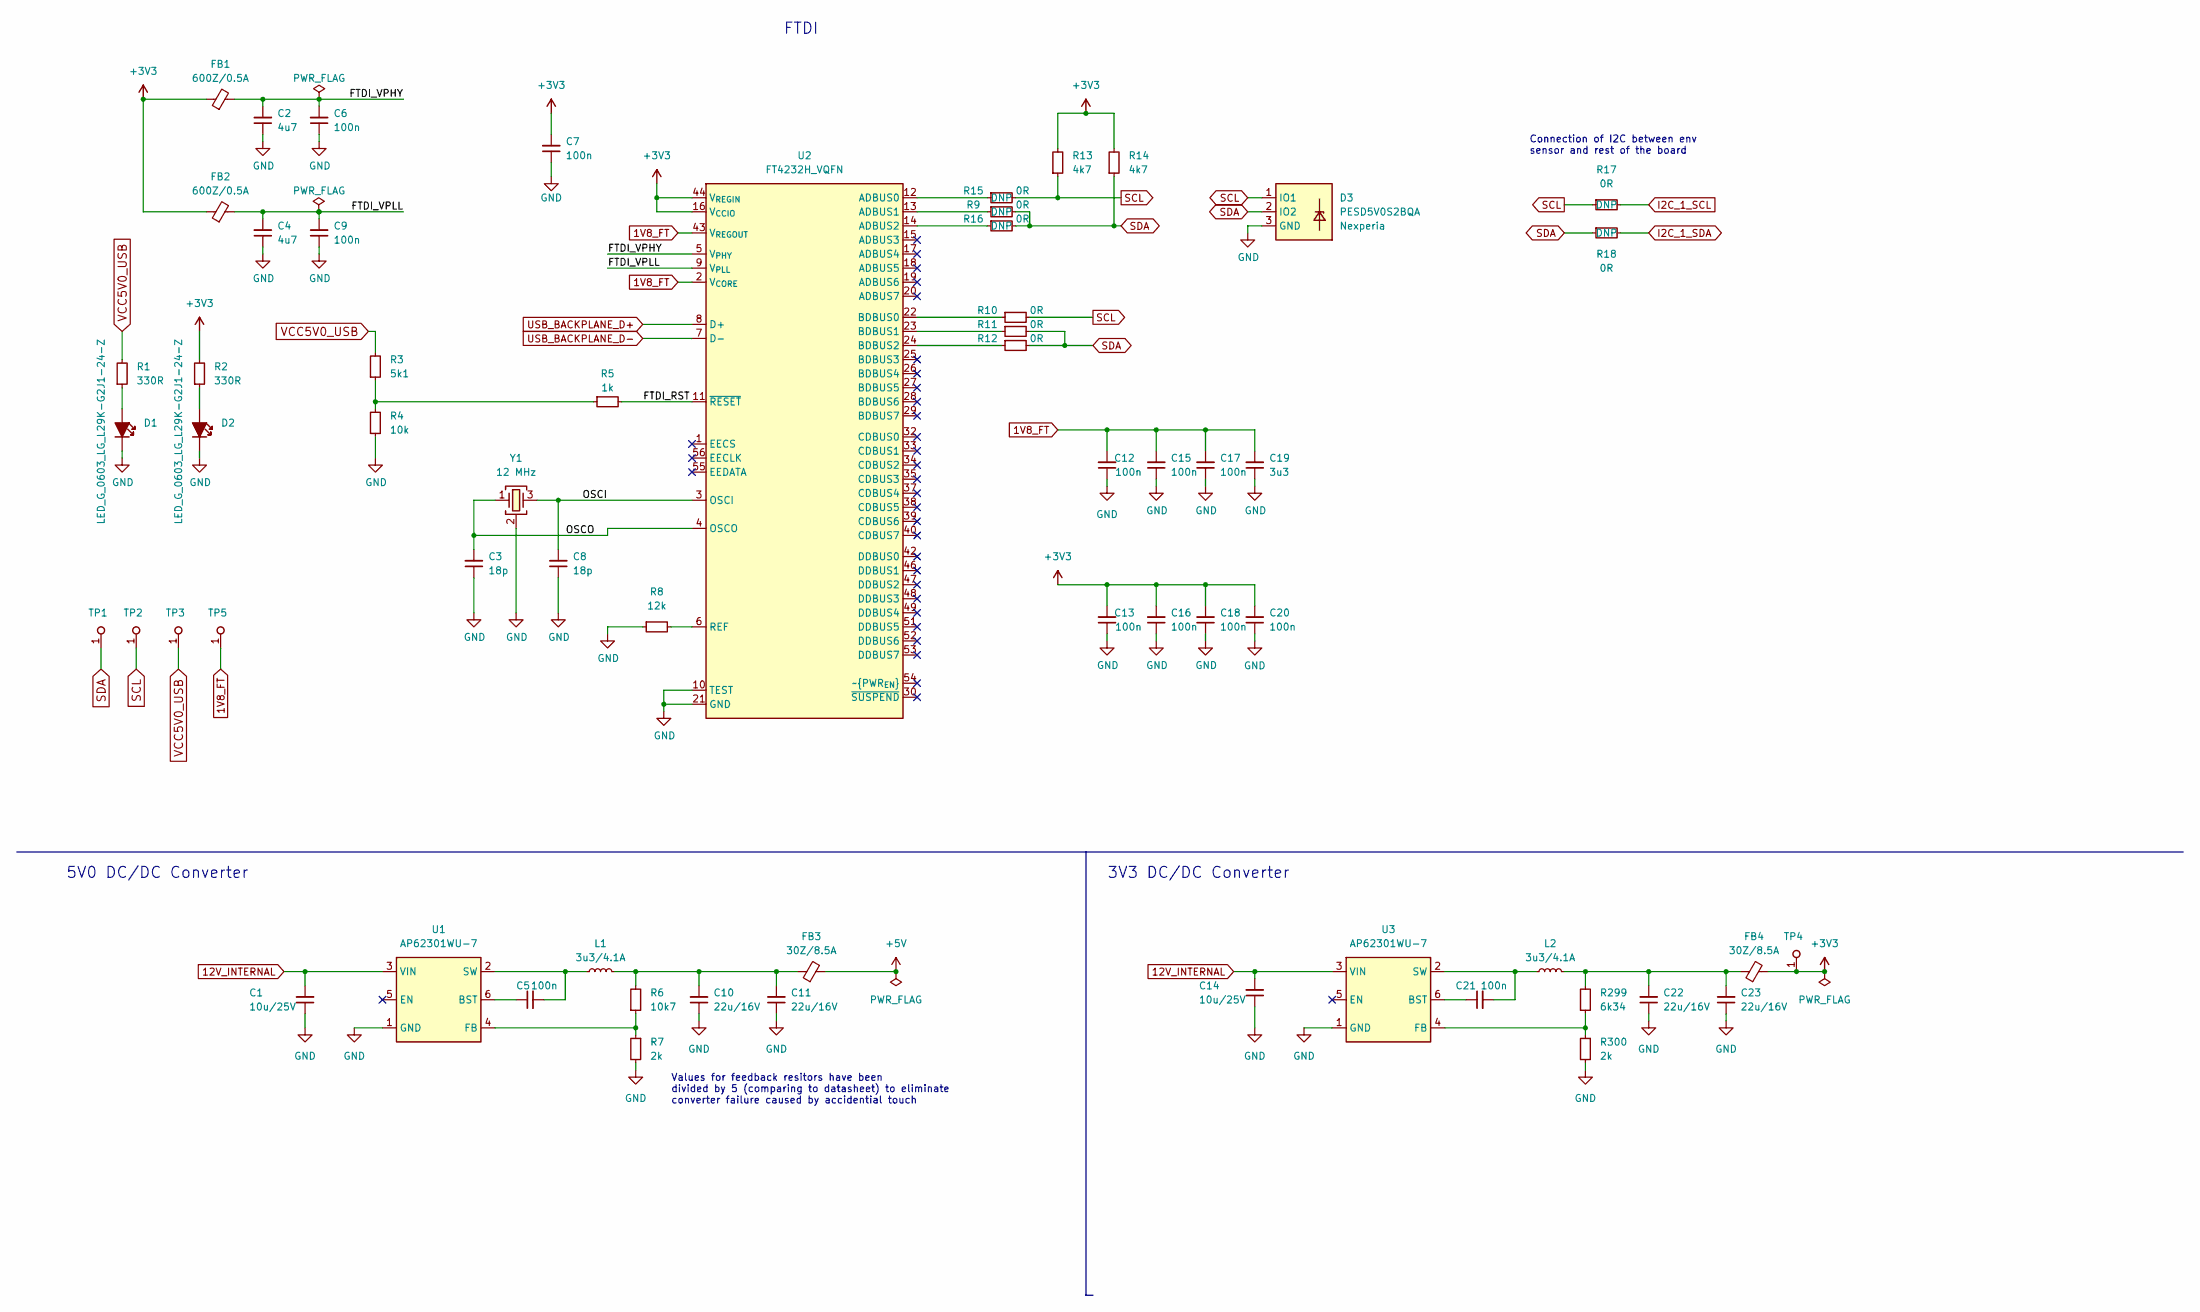
[picture p32: schematic ftdi-module.kicad_sch]

Parts:
C1, C14: C_10u_25V_0603; C_0603_1608Metric; MPN C1608X5R1E106M080AC
C2, C4: C_4u7_0402; C_0402_1005Metric; MPN GRM155R61A475MEAAD
C3, C8: C_18p_0402; C_0402_1005Metric; MPN CL05C180JB51PNC
C5, C6, C7, C9, C12, C13, C15, C16, C17, C18, C20, C21: C_100n_0402; C_0402_1005Metric; Voltage 50V; MPN GRM155R61H104KE14D
C10, C11, C22, C23: C_22u_16V_0603; C_0603_1608Metric; MPN CL10A226MO7JZNC
C19: C_3u3_0402; C_0402_1005Metric; MPN C1005JB1A335K050BC
D1, D2: LED_G_0603_LG_L29K-G2J1-24-Z; LED_0603_1608Metric_G; MPN LG L29K-G2J1-24-Z
D3: PESD5V0S2BQA; TPD2E009DRTR; MPN PESD5V0S2BQA
FB1, FB2: FB_600Z_0.5A_Murata-BLM18AG_0603; FB_0603_1608Metric; MPN BLM18AG601SN1D
FB3, FB4: FB_30Z_8.5A_Murata-BLM21SN_0805; FB_0805_2012Metric; MPN BLM21SN300SZ1D
L1, L2: L_3u3_4.1A_WE-LHMI-5030; L_WE-LHMI-5030; MPN 74437336033
R1, R2: R_330R_0402; R_0402_1005Metric; Tolerance 1%; MPN CR0402-FX-3300GLF
R3: R_5k1_0402; R_0402_1005Metric; Tolerance 1%; MPN CR0402-FX-5101GLF
R4: R_10k_0402; R_0402_1005Metric; Tolerance 1%; MPN CR0402-FX-1002GLF
R5: R_1k_0402; R_0402_1005Metric; Tolerance 1%; MPN CR0402-FX-1001GLF
R6: R_10k7_0402; R_0402_1005Metric; Tolerance 1%; MPN CR0402-FX-1072GLF
R7, R300: R_2k_0402; R_0402_1005Metric; Tolerance 1%; MPN CR0402-FX-2001GLF
R8: R_12k_0402; R_0402_1005Metric; Tolerance 1%; MPN CR0402-FX-1202GLF
R9, R10, R11, R12, R15, R16, R17, R18: R_0R_0402; R_0402_1005Metric; MPN ERJ2GE0R00X
R13, R14: R_4k7_0402; R_0402_1005Metric; Tolerance 1%; MPN CR0402-FX-4701GLF
R299: R_6k34_0402; R_0402_1005Metric; Tolerance 1%; MPN CR0402-FX-6341GLF
TP1, TP2, TP3, TP4, TP5: TP_1mm_SMD; TP_SMD_1mm
U1, U3: AP62301_TSOT; TSOT23-6; MPN AP62301WU-7
U2: FT4232H_VQFN; QFN-56-1EP_8x8mm_P0.5mm; MPN FT4232H-56Q-REEL
Y1: Resonator_12MHz_ABM8G; Oscillator_SMD_Geyer_KX-7-4Pin_3.2x2.5mm; MPN ABM8G-12.000MHZ-18-D2Y-T

Connections:
1V8_FT: C12.2, C15.2, C17.2, C19.2, TP5.1, U2.2 (V_{CORE}), U2.31 (V_{CORE}), U2.43 (V_{REGOUT})
12V_INTERNAL: C1.2, C14.2, U1.3 (VIN), U3.3 (VIN)
+3V3: C7.2, C13.2, C16.2, C18.2, C20.2, FB1.1, FB2.1, FB4.2, R2.2, R13.2, R14.2, TP4.1, U2.16 (V_{CCIO}), U2.36 (V_{CCIO}), U2.44 (V_{REGIN}), U2.50 (V_{CCIO})
+5V: FB3.2
FTDI_RST: R5.2, U2.11 (~RESET)
FTDI_VPHY: C2.2, C6.2, FB1.2, U2.5 (V_{PHY})
FTDI_VPLL: C4.2, C9.2, FB2.2, U2.9 (V_{PLL})
GND: C1.1, C2.1, C3.1, C4.1, C6.1, C7.1, C8.1, C9.1, C10.1, C11.1, C12.1, C13.1, C14.1, C15.1, C16.1, C17.1, C18.1, C19.1, C20.1, C22.1, C23.1, D1.2, D2.2, D3.3 (GND), R4.1, R7.2, R8.1, R300.2, U1.1 (GND), U2.10 (TEST), U2.21 (GND), U2.41 (GND), U2.45 (GND), U2.57 (GND), U3.1 (GND), Y1.2 (SH), Y1.4 (SH)
I2C_1_SCL: R17.2
I2C_1_SDA: R18.2
unnamed: C5.1, U1.6 (BST)
unnamed: C5.2, L1.1, U1.2 (SW)
unnamed: C10.2, C11.2, FB3.1, L1.2, R6.2
unnamed: C21.1, U3.6 (BST)
unnamed: C21.2, L2.1, U3.2 (SW)
unnamed: C22.2, C23.2, FB4.1, L2.2, R299.2
unnamed: D1.1, R1.1
unnamed: D2.1, R2.1
unnamed: R3.1, R4.2, R5.1
unnamed: R6.1, R7.1, U1.4 (FB)
unnamed: R8.2, U2.6 (REF)
unnamed: R9.1, U2.13 (ADBUS1)
unnamed: R10.1, U2.22 (BDBUS0)
unnamed: R11.1, U2.23 (BDBUS1)
unnamed: R12.1, U2.24 (BDBUS2)
unnamed: R15.1, U2.12 (ADBUS0)
unnamed: R16.1, U2.14 (ADBUS2)
unnamed: R299.1, R300.1, U3.4 (FB)
OSCI: C8.2, U2.3 (OSCI), Y1.3
OSCO: C3.2, U2.4 (OSCO), Y1.1
SCL: D3.1 (IO1), R10.2, R13.1, R15.2, R17.1, TP2.1
SDA: D3.2 (IO2), R9.2, R11.2, R12.2, R14.1, R16.2, R18.1, TP1.1
USB_BACKPLANE_D+: U2.8 (D+)
USB_BACKPLANE_D-: U2.7 (D-)
VCC5V0_USB: R1.2, R3.2, TP3.1

Notes on the sheet:
3V3 DC/DC Converter
Connection of I2C between env sensor and rest of the board
FTDI
Values for feedback resitors have been divided by 5 (comparing to datasheet) to eliminate converter failure caused by accidential touch
5V0 DC/DC Converter
