antmicro/gpu-cluster-backplane/gpu-cluster-backplane.kicad_sch

## KiCad design gpu-cluster-backplane.kicad_sch (2023-11-16)

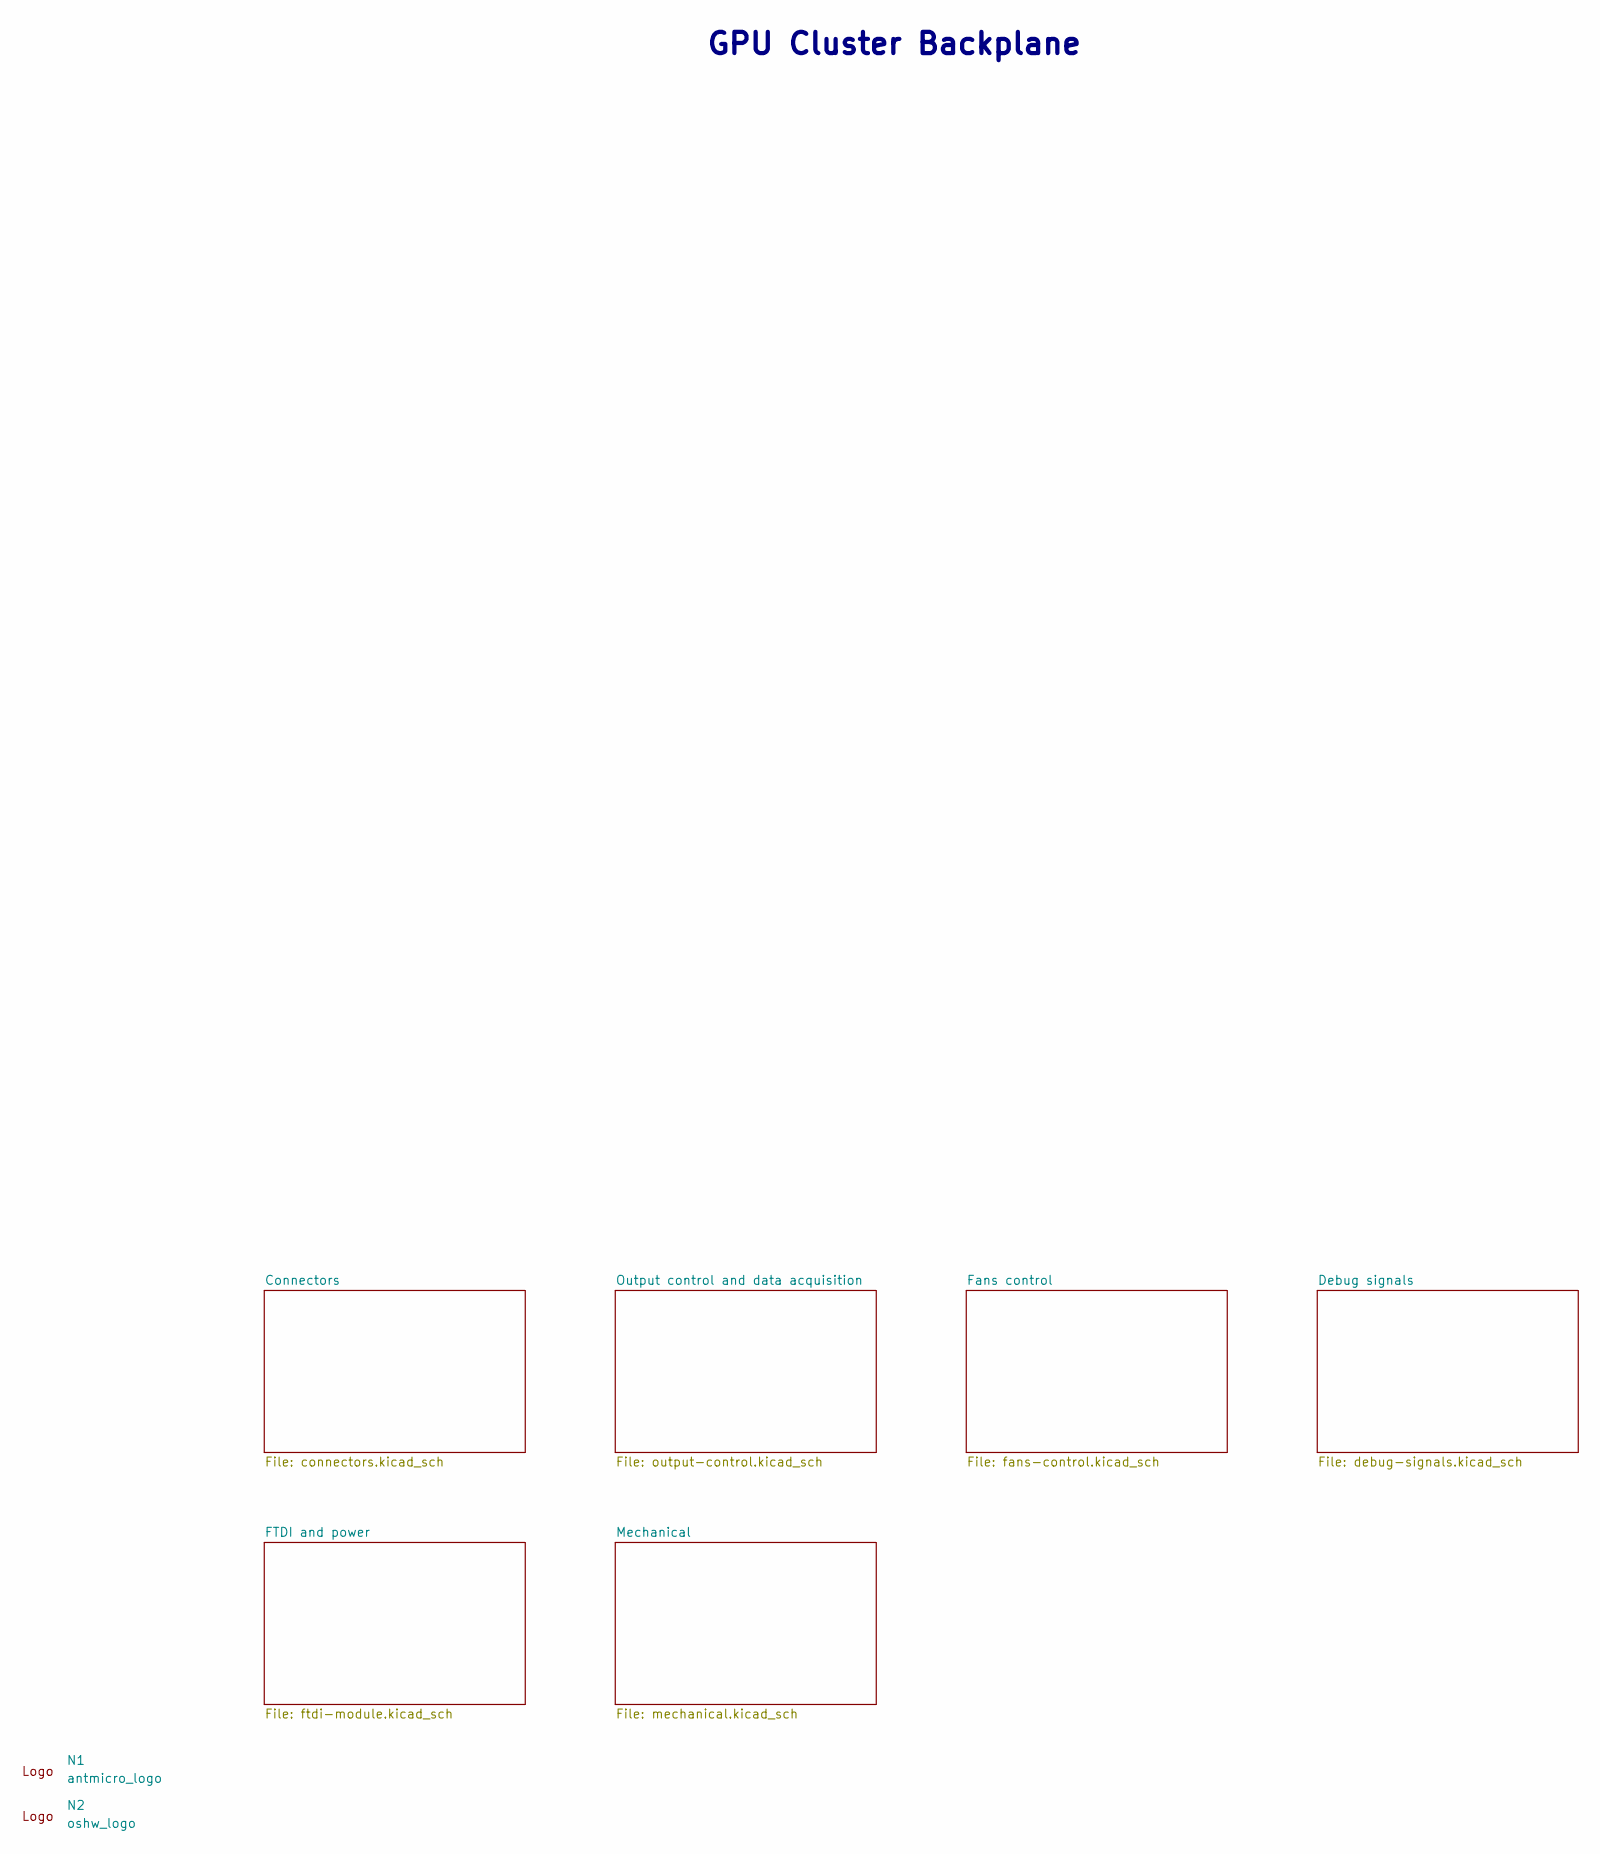
[picture p33: schematic gpu-cluster-backplane.kicad_sch]

Parts:
N1: antmicro_logo; antmicro-logo
N2: oshw_logo; oshw-logo

Notes on the sheet:
GPU Cluster Backplane
