antmicro/gpu-cluster-backplane/mechanical.kicad_sch

## KiCad design mechanical.kicad_sch (2023-11-16)

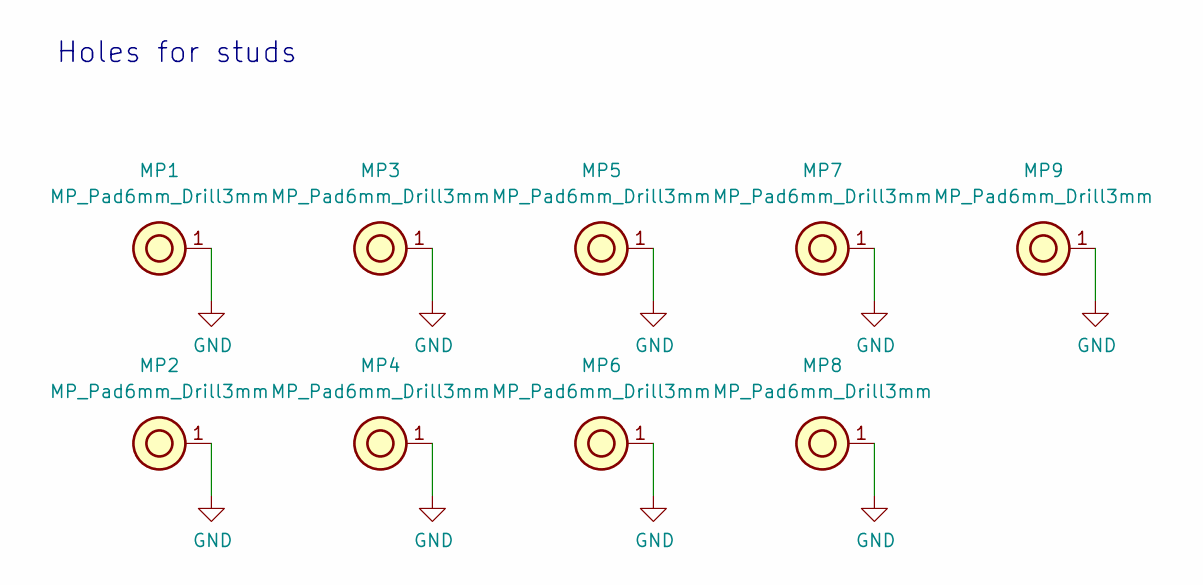
[picture p34: schematic mechanical.kicad_sch]

Parts:
MP1, MP2, MP3, MP4, MP5, MP6, MP7, MP8, MP9: MP_Pad6mm_Drill3mm

Connections:
GND: MP1.1, MP2.1, MP3.1, MP4.1, MP5.1, MP6.1, MP7.1, MP8.1, MP9.1

Notes on the sheet:
Holes for studs
