antmicro/gpu-cluster-backplane/output-control.kicad_sch

## KiCad design output-control.kicad_sch (2023-11-15)

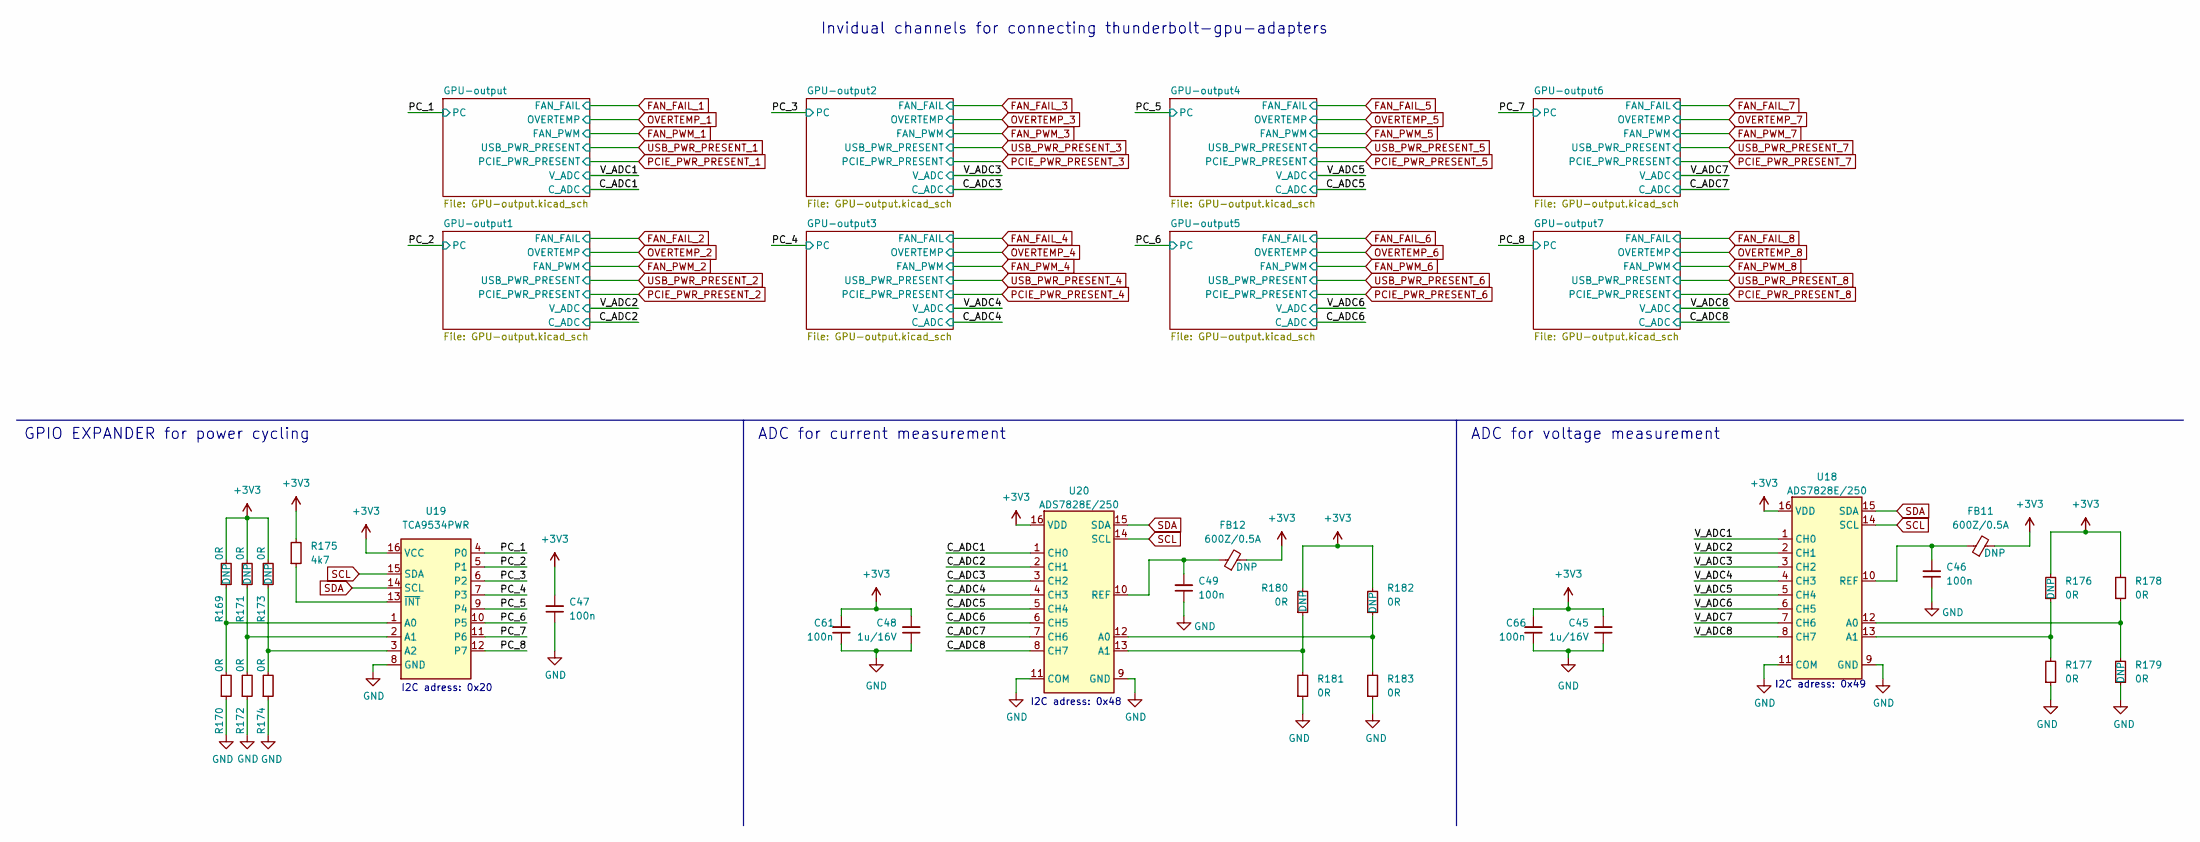
[picture p35: schematic output-control.kicad_sch]

Parts:
C45, C48: C_1u_16V_0402; C_0402_1005Metric; MPN C0402C105M4PACTU
C46, C47, C49, C61, C66: C_100n_0402; C_0402_1005Metric; Voltage 50V; MPN GRM155R61H104KE14D
FB11, FB12: FB_600Z_0.5A_Murata-BLM18AG_0603; FB_0603_1608Metric; MPN BLM18AG601SN1D
R169, R170, R171, R172, R173, R174, R176, R177, R178, R179, R180, R181, R182, R183: R_0R_0402; R_0402_1005Metric; MPN ERJ2GE0R00X
R175: R_4k7_0402; R_0402_1005Metric; Tolerance 1%; MPN CR0402-FX-4701GLF
U18, U20: ADS7828; TSSOP-16_4.4x5mm_P0.65mm; MPN ADS7828E/250
U19: TCA9534PWR_TSSOP; TSSOP-16_4.4x5mm_P0.65mm; MPN TCA9534PWR

Connections:
+3V3: C45.2, C47.2, C48.2, C61.2, C66.2, FB11.2, FB12.2, R169.2, R171.2, R173.2, R175.2, R176.2, R178.2, R180.2, R182.2, U18.16 (VDD), U19.16 (VCC), U20.16 (VDD)
C_ADC1: U20.1 (CH0)
C_ADC2: U20.2 (CH1)
C_ADC3: U20.3 (CH2)
C_ADC4: U20.4 (CH3)
C_ADC5: U20.5 (CH4)
C_ADC6: U20.6 (CH5)
C_ADC7: U20.7 (CH6)
C_ADC8: U20.8 (CH7)
GND: C45.1, C46.1, C47.1, C48.1, C49.1, C61.1, C66.1, R170.1, R172.1, R174.1, R177.1, R179.1, R181.1, R183.1, U18.9 (GND), U18.11 (COM), U19.8 (GND), U20.9 (GND), U20.11 (COM)
unnamed: C46.2, FB11.1, U18.10 (REF)
unnamed: C49.2, FB12.1, U20.10 (REF)
unnamed: R169.1, R170.2, U19.1 (A0)
unnamed: R171.1, R172.2, U19.2 (A1)
unnamed: R173.1, R174.2, U19.3 (A2)
unnamed: R175.1, U19.13 (~INT)
unnamed: R176.1, R177.2, U18.13 (A1)
unnamed: R178.1, R179.2, U18.12 (A0)
unnamed: R180.1, R181.2, U20.13 (A1)
unnamed: R182.1, R183.2, U20.12 (A0)
PC_1: U19.4 (P0)
PC_2: U19.5 (P1)
PC_3: U19.6 (P2)
PC_4: U19.7 (P3)
PC_5: U19.9 (P4)
PC_6: U19.10 (P5)
PC_7: U19.11 (P6)
PC_8: U19.12 (P7)
SCL: U18.14 (SCL), U19.15 (SDA), U20.14 (SCL)
SDA: U18.15 (SDA), U19.14 (SCL), U20.15 (SDA)
V_ADC1: U18.1 (CH0)
V_ADC2: U18.2 (CH1)
V_ADC3: U18.3 (CH2)
V_ADC4: U18.4 (CH3)
V_ADC5: U18.5 (CH4)
V_ADC6: U18.6 (CH5)
V_ADC7: U18.7 (CH6)
V_ADC8: U18.8 (CH7)

Notes on the sheet:
I2C adress: 0x48
GPIO EXPANDER for power cycling
ADC for current measurement
ADC for voltage measurement
Invidual channels for connecting thunderbolt-gpu-adapters
I2C adress: 0x49
I2C adress: 0x20
